svpetry/SP-C64/Keyboard/Chameleon_64_-_PS2_Keymap.jpg

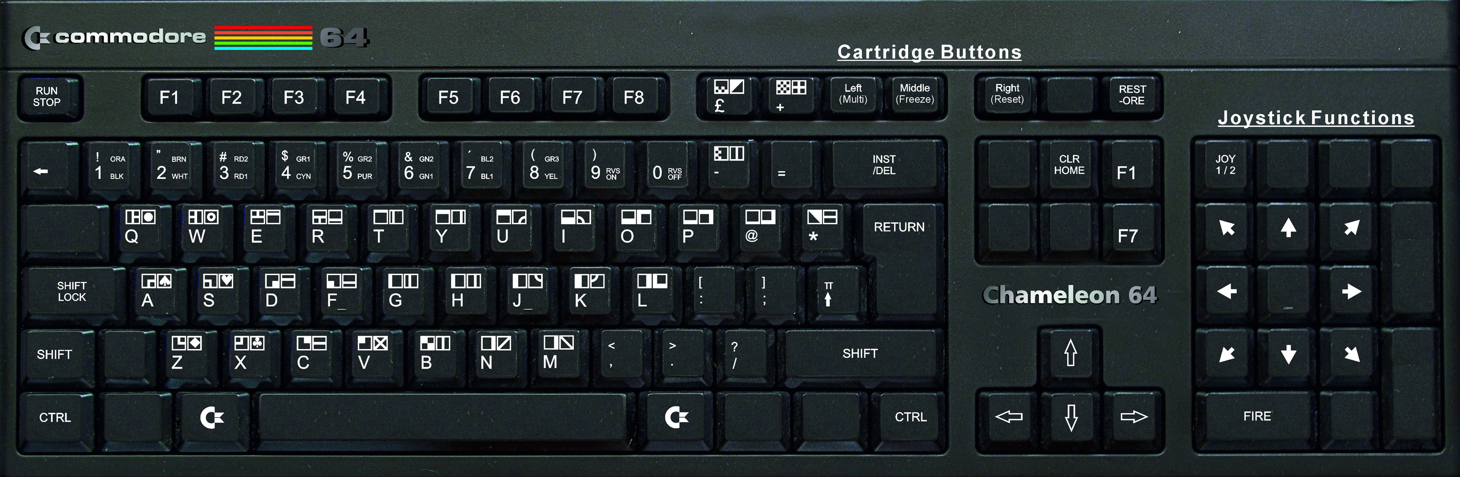
Keyboard/Chameleon_64_-_PS2_Keymap.jpg
