svpetry/SP-C64/CIA/6526-1.gif

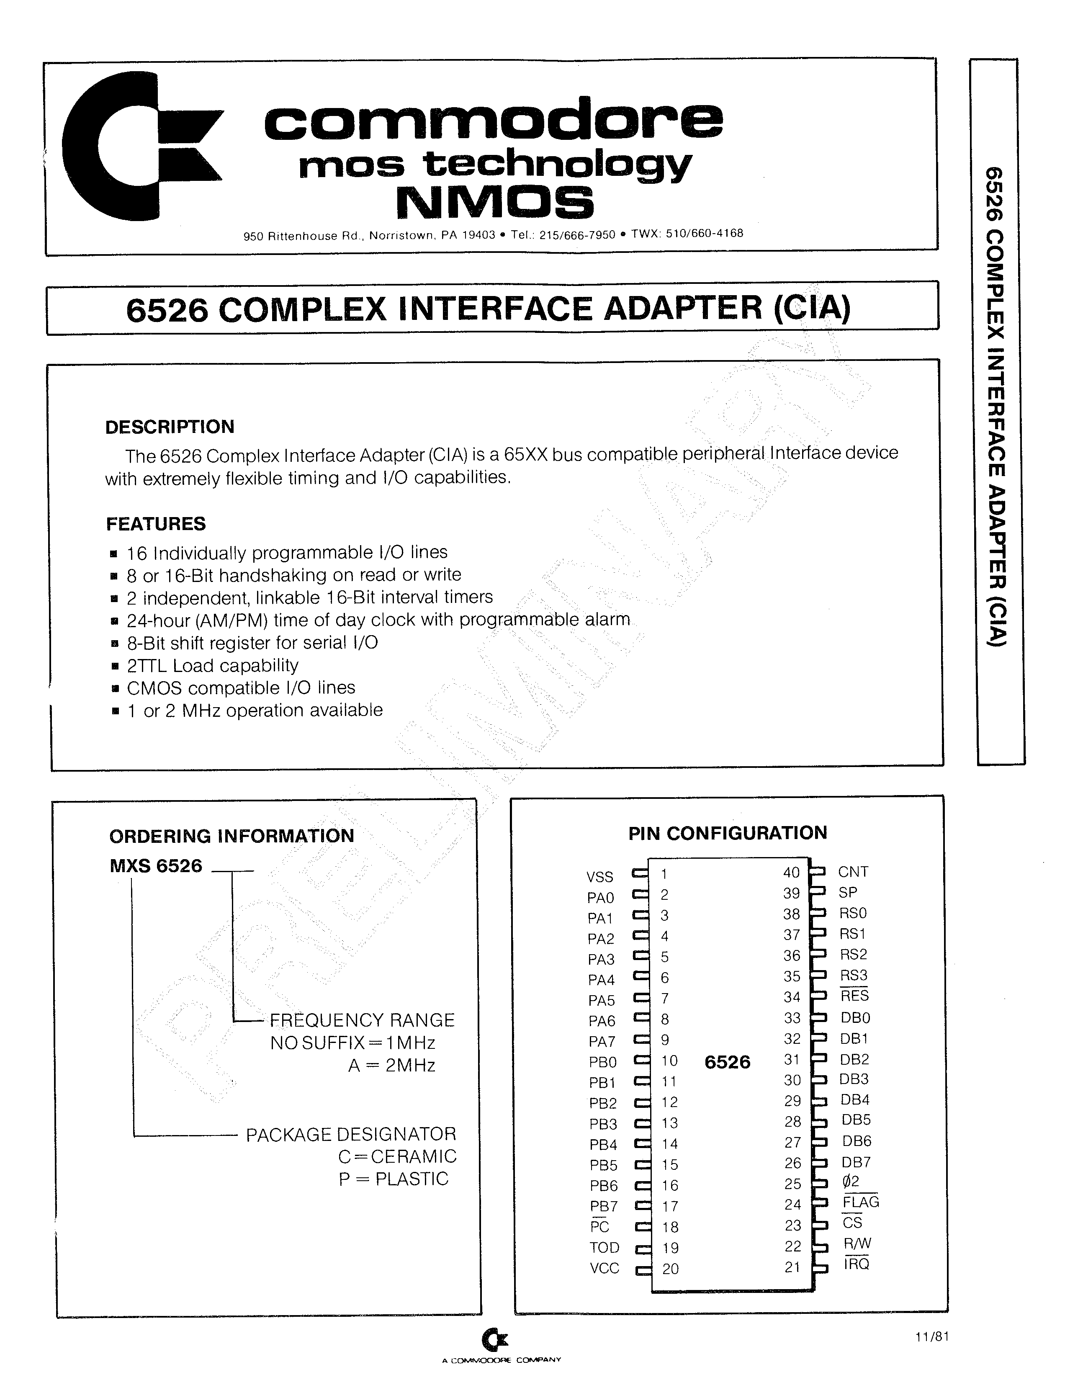
CIA/6526-1.gif
