svpetry/SP-C64/CIA/6526-2.gif

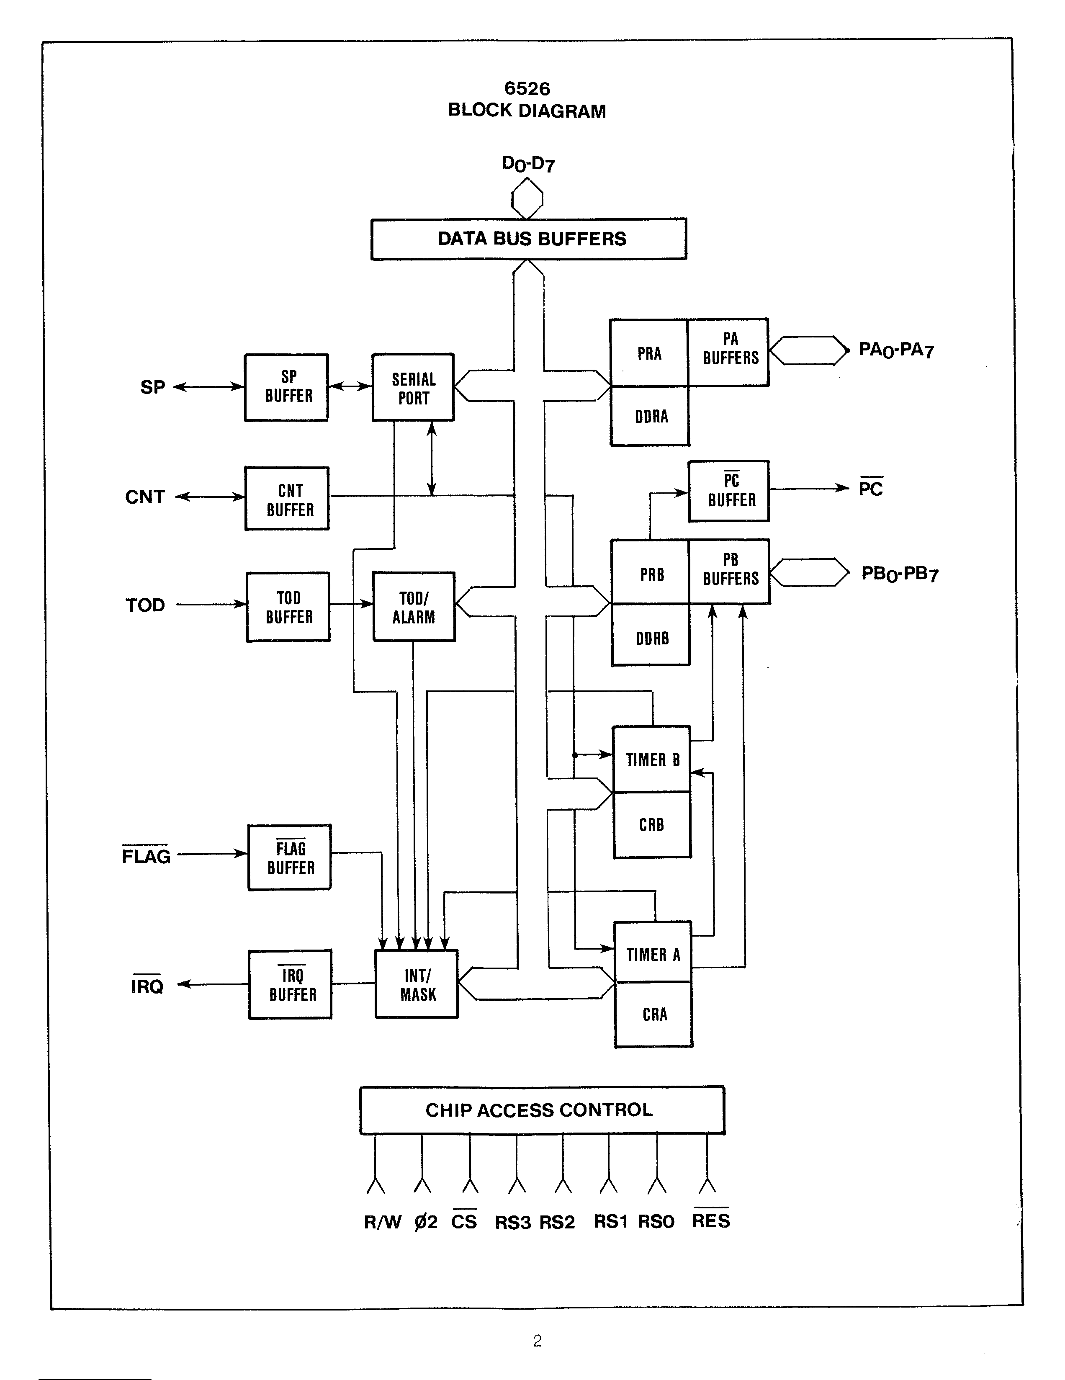
CIA/6526-2.gif
