svpetry/SP-C64/CIA/6526-3.gif

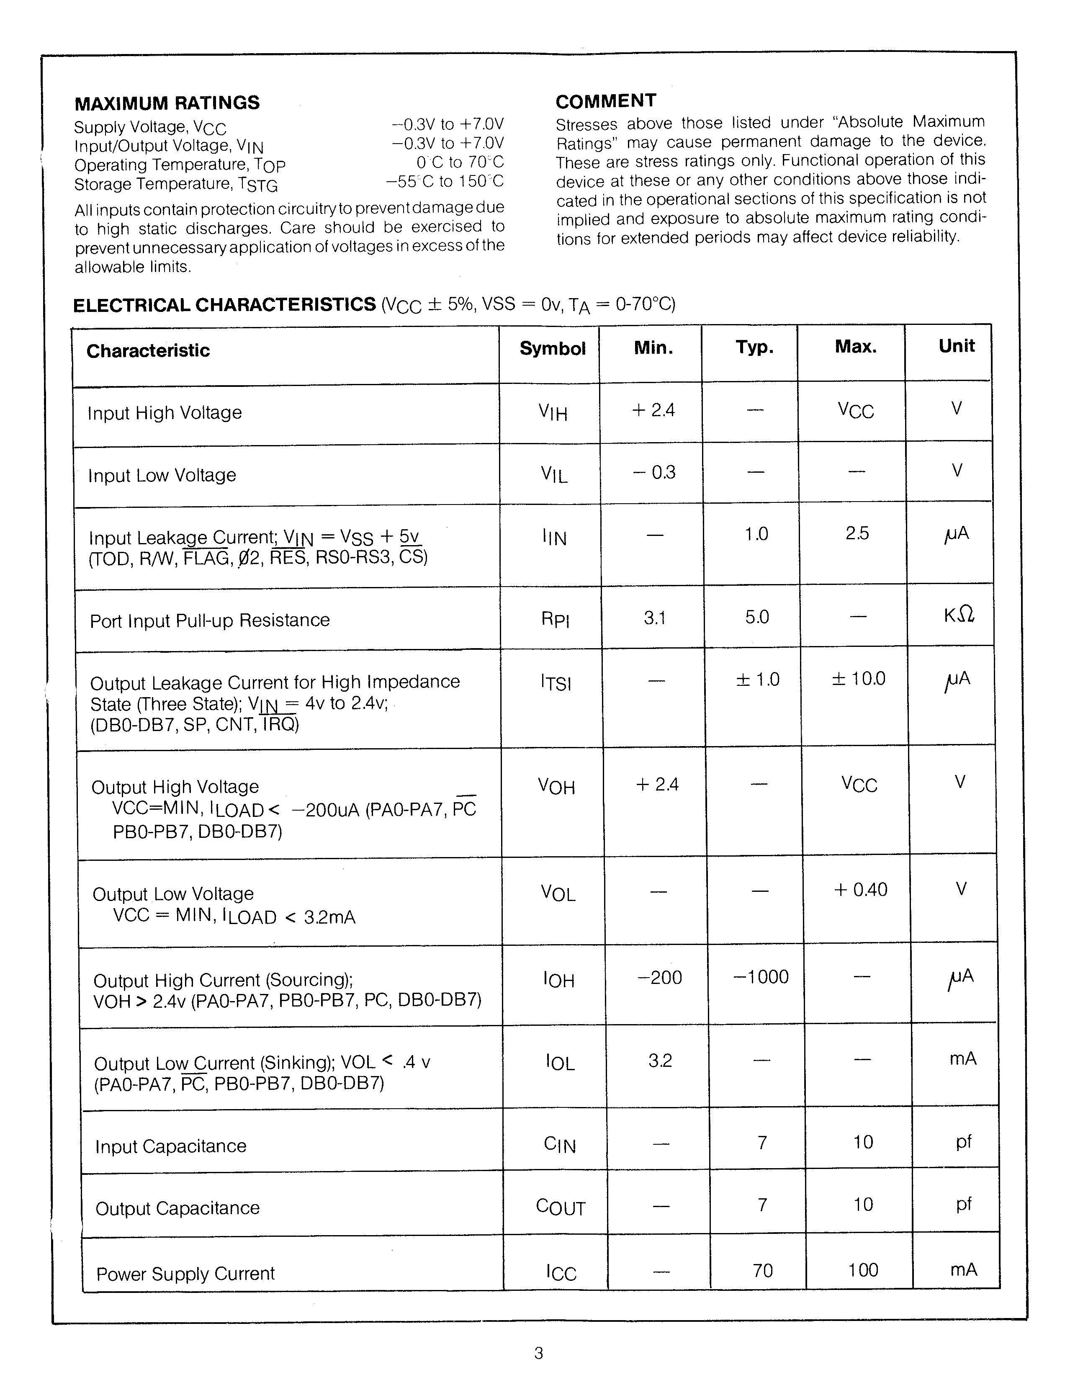
CIA/6526-3.gif
