svpetry/SP-C64/CIA/6526-4.gif

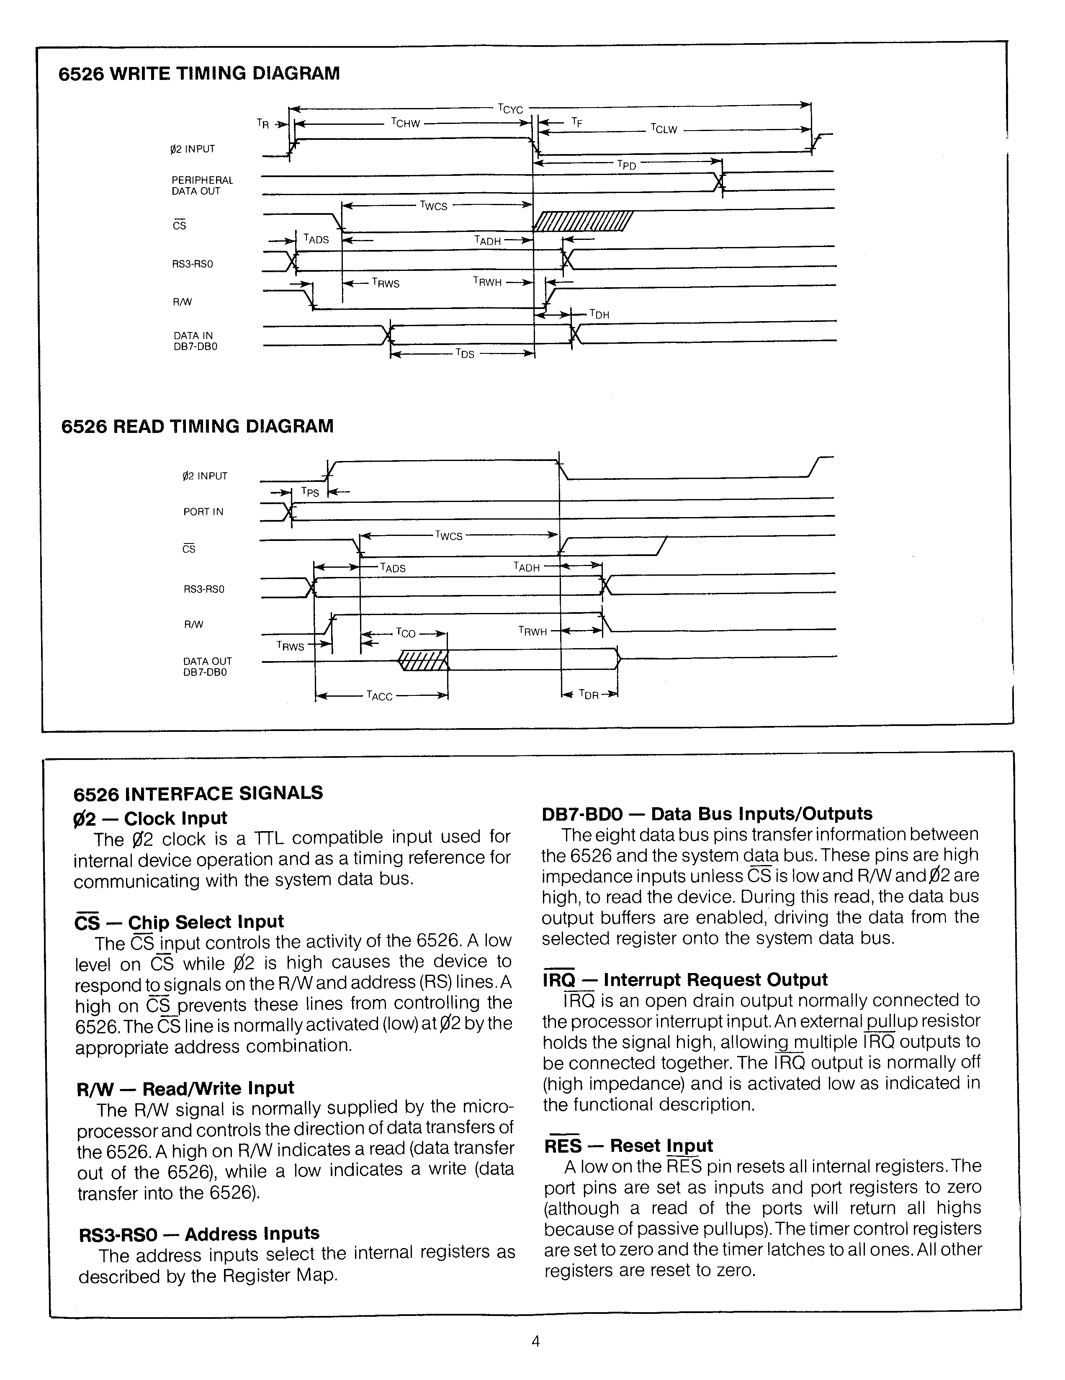
CIA/6526-4.gif
