svpetry/SP-C64/CIA/6526-5.gif

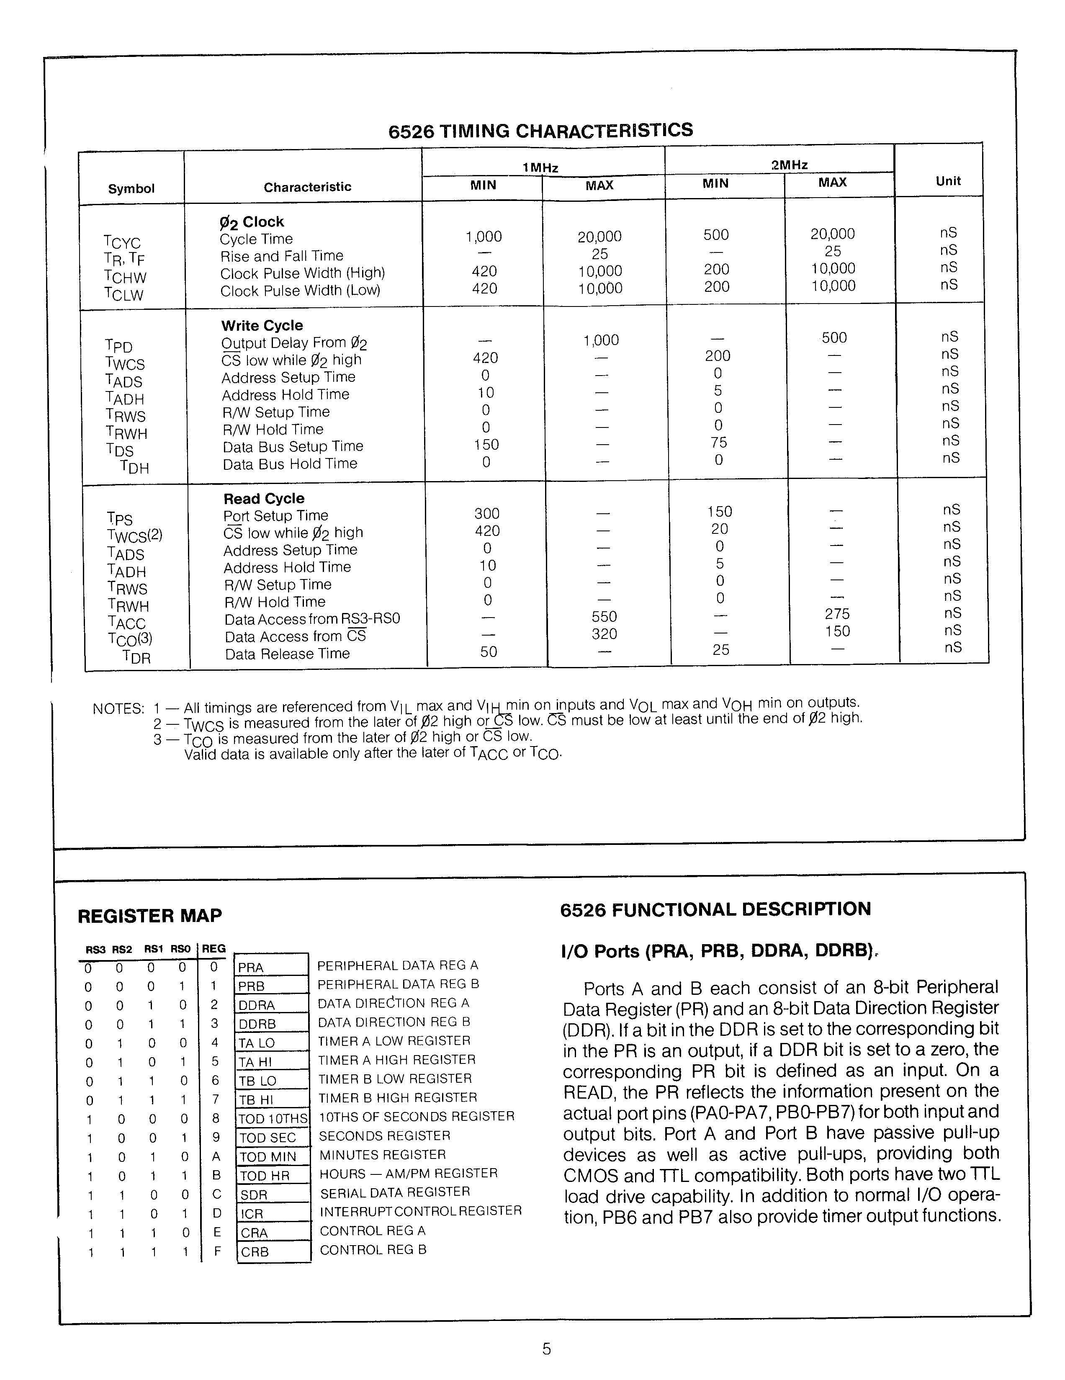
CIA/6526-5.gif
