svpetry/SP-C64/CIA/6526-6.gif

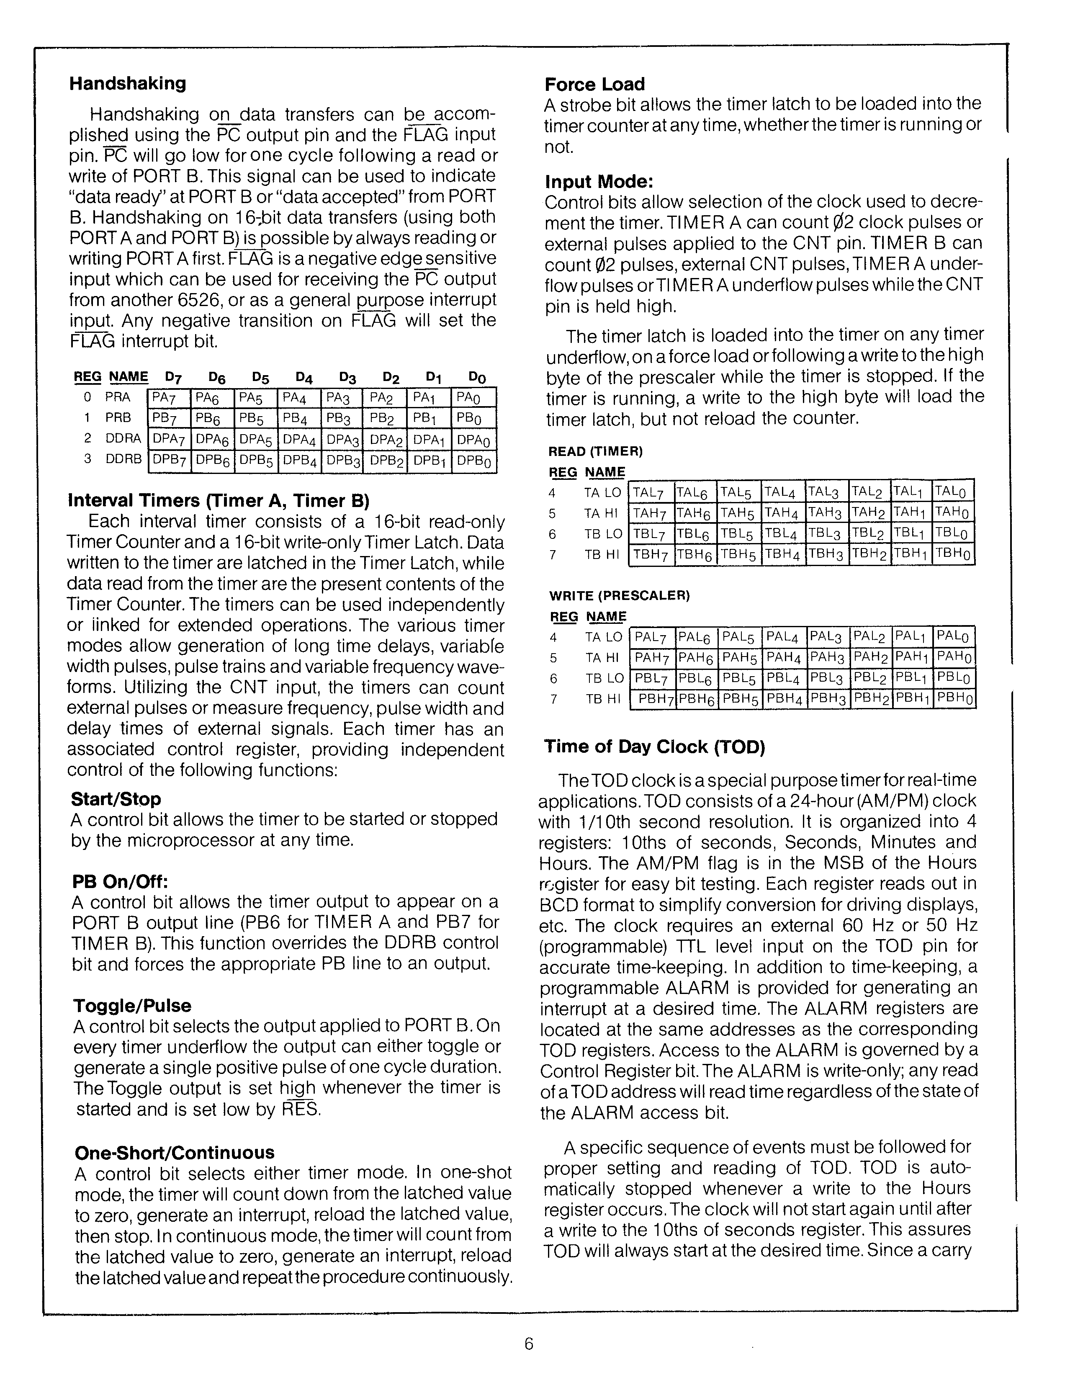
CIA/6526-6.gif
