svpetry/SP-C64/CIA/6526-7.gif

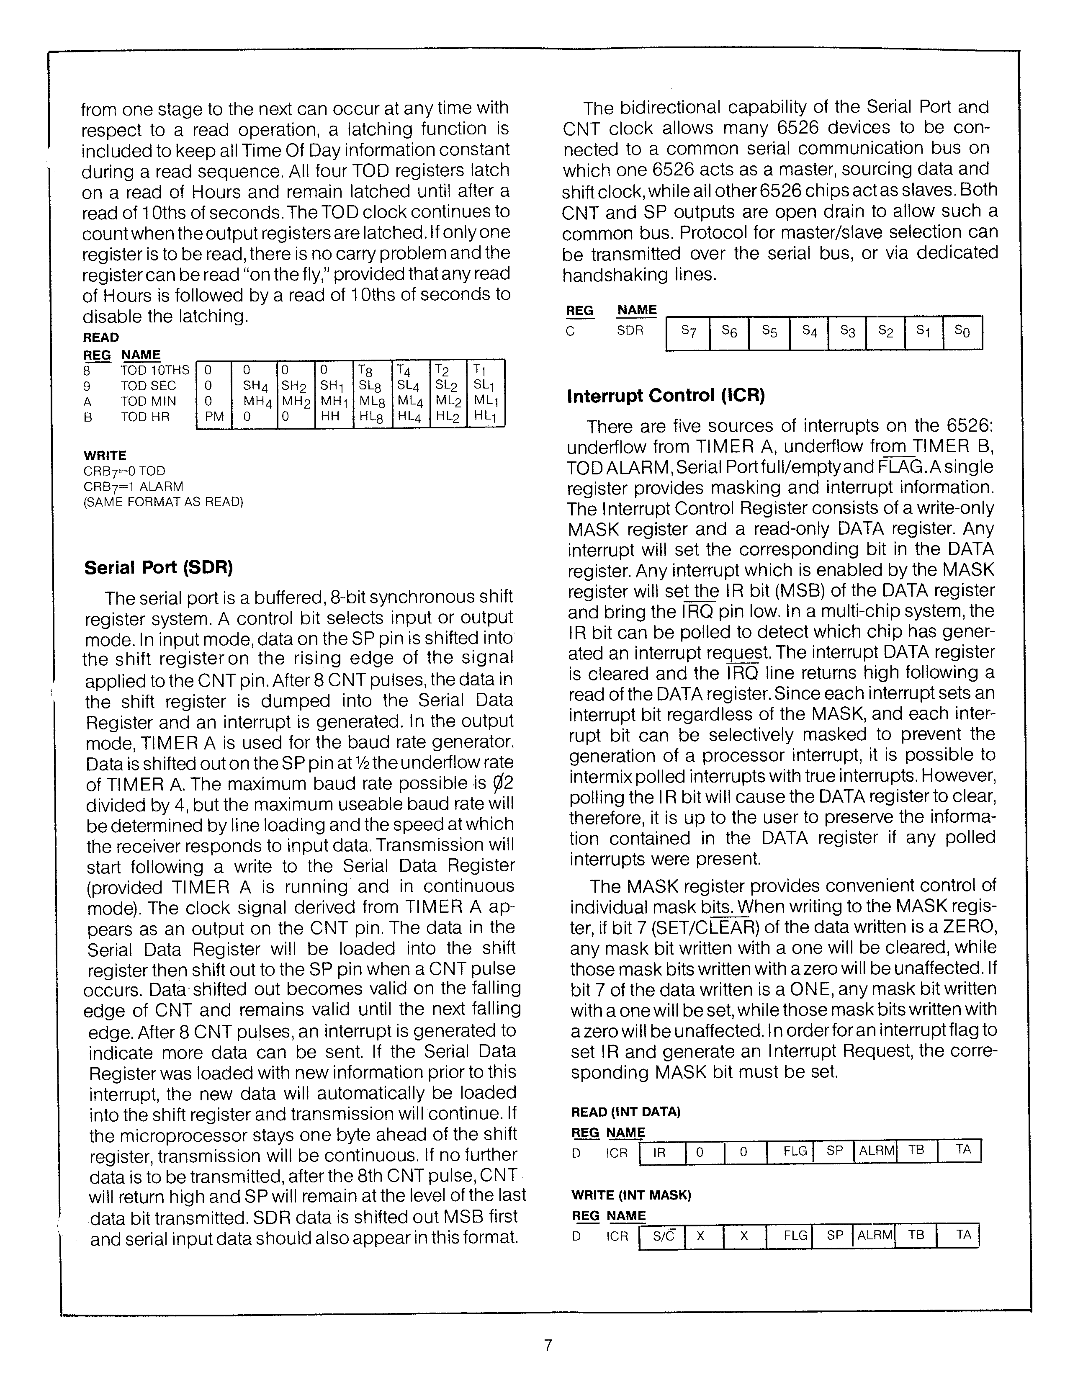
CIA/6526-7.gif
