svpetry/SP-C64/CIA/6526-8.gif

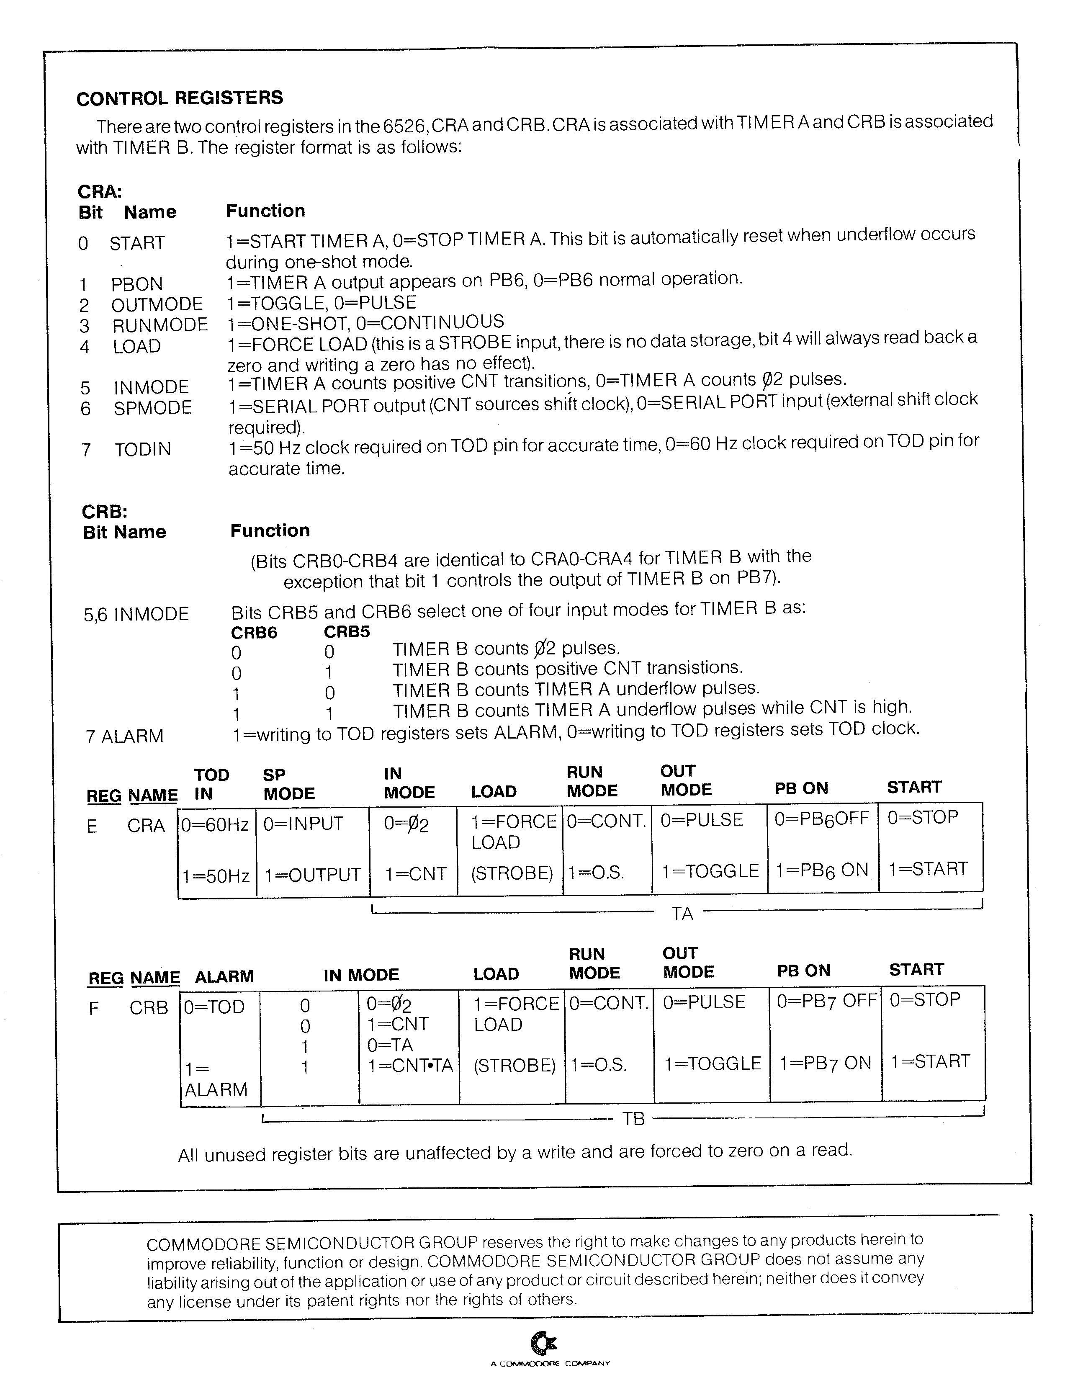
CIA/6526-8.gif
