svpetry/SP-C64/CIA/13114.png

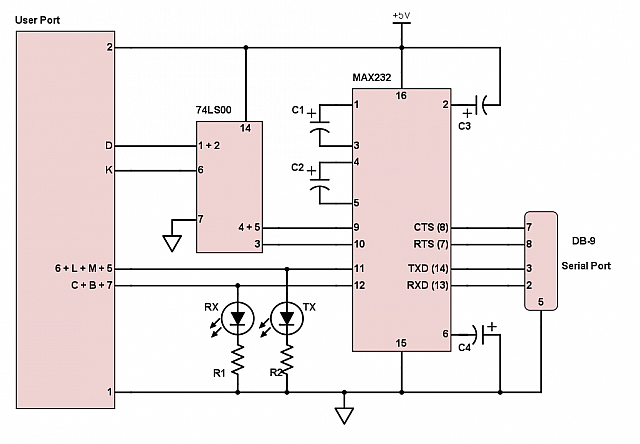
CIA/13114.png
