svpetry/SP-C64/Diagnostic/C64_Diagnostic_324517-02/C64_Diagnostic_324517-02.png

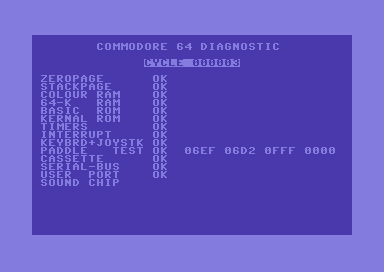
Diagnostic/C64_Diagnostic_324517-02/C64_Diagnostic_324517-02.png
