svpetry/SP-C64/Diagnostic/C64_Diagnostic_324517-02/C64_Diagnostic_schematic.jpg

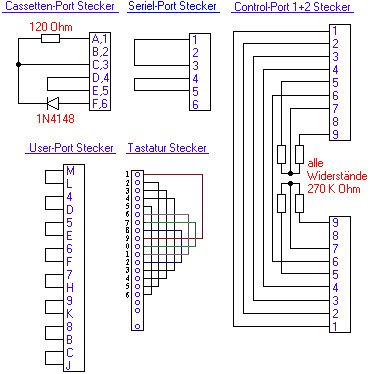
Diagnostic/C64_Diagnostic_324517-02/C64_Diagnostic_schematic.jpg
