svpetry/SP-C64/Diagnostic/Diag_586220/C64_Diag_586220_Harness_schem1.png

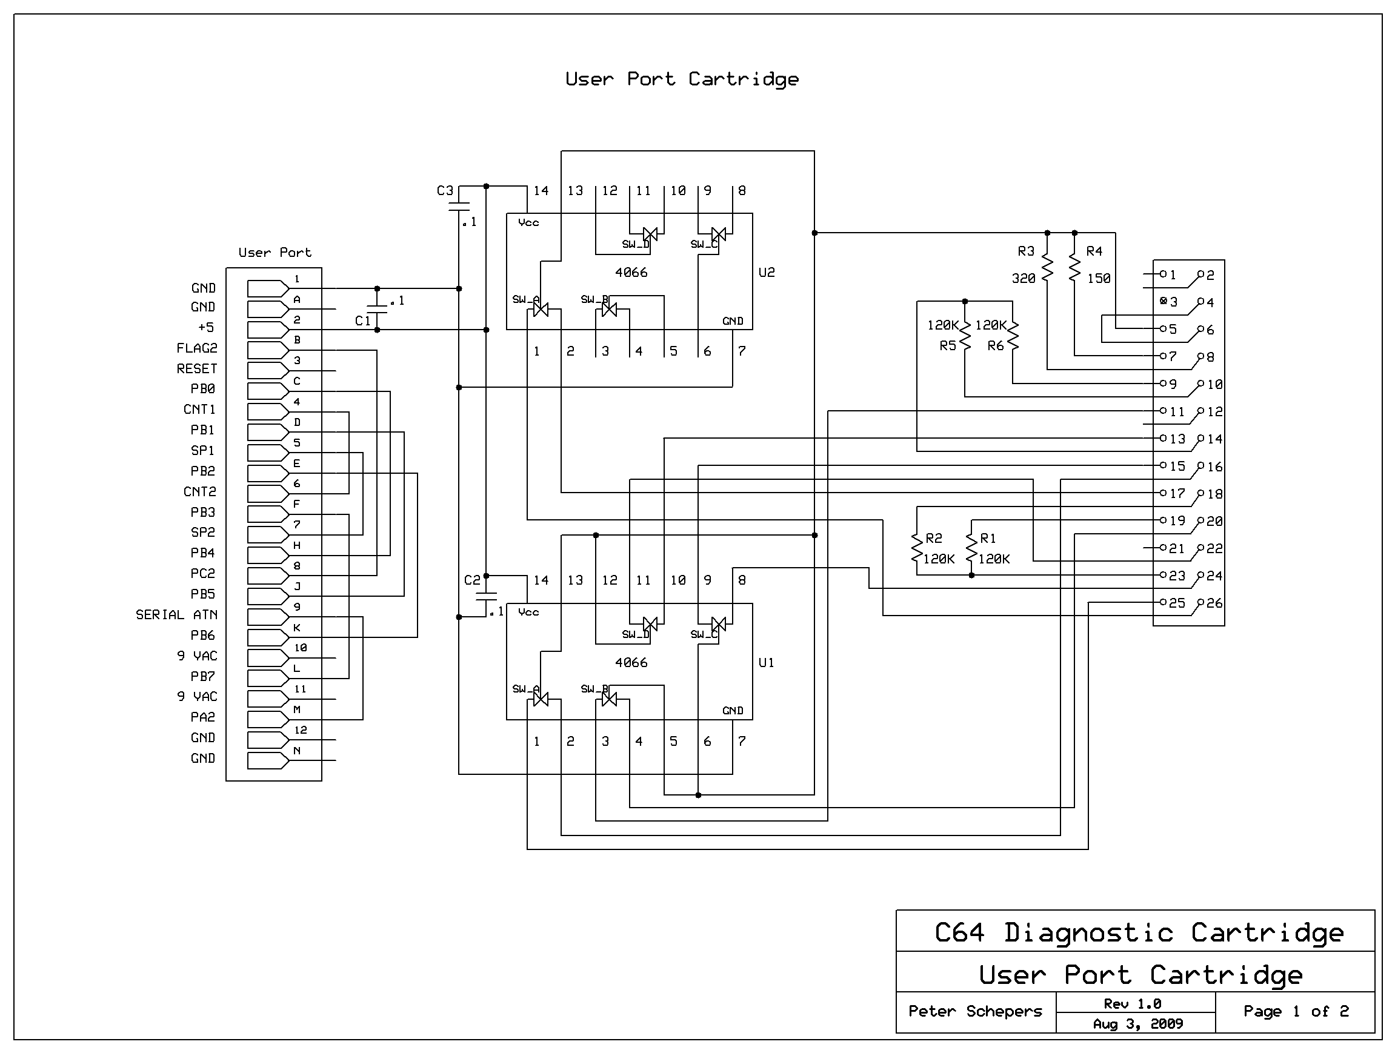
Diagnostic/Diag_586220/C64_Diag_586220_Harness_schem1.png
