svpetry/SP-C64/Diagnostic/Diag_586220/diag-c64_586220.png

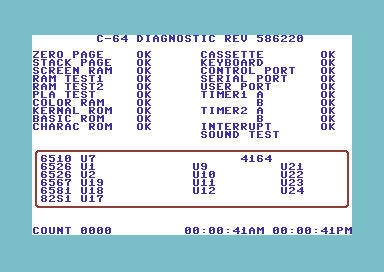
Diagnostic/Diag_586220/diag-c64_586220.png
