svpetry/SP-C64/Keyboard/keybconn.gif

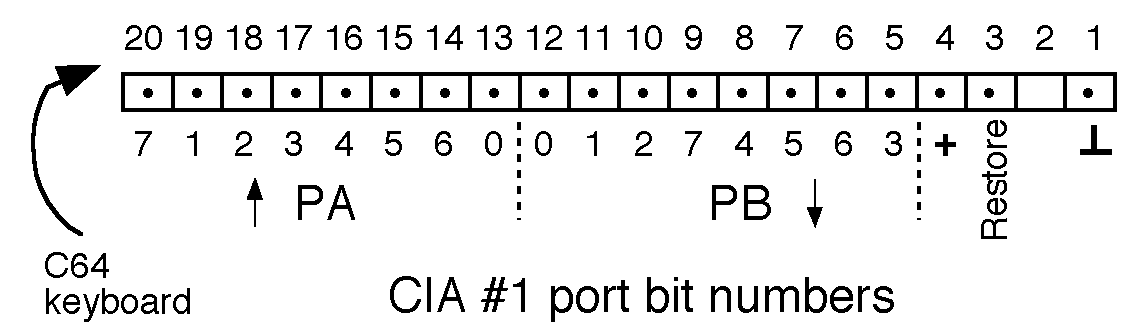
Keyboard/keybconn.gif
