svpetry/SP-C64/Keyboard/scancod1.gif

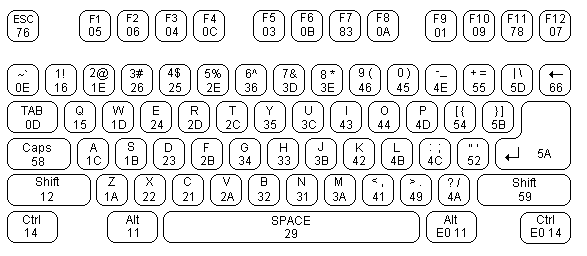
Keyboard/scancod1.gif
