svpetry/SP-C64/Keyboard/scancodes.gif

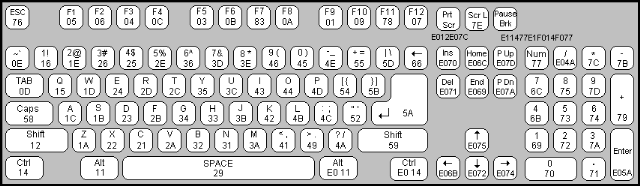
Keyboard/scancodes.gif
