svpetry/SP-C64/Keyboard/uskeyb.gif

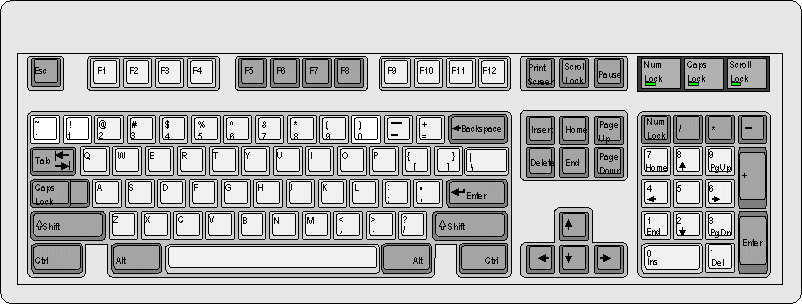
Keyboard/uskeyb.gif
