svpetry/SP-C64/PLA/PLA_IO.png

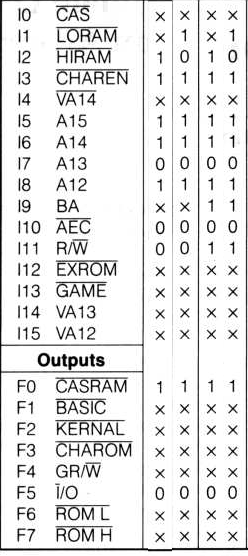
PLA/PLA_IO.png
