svpetry/SP-C64/RAM/georam-sch.png

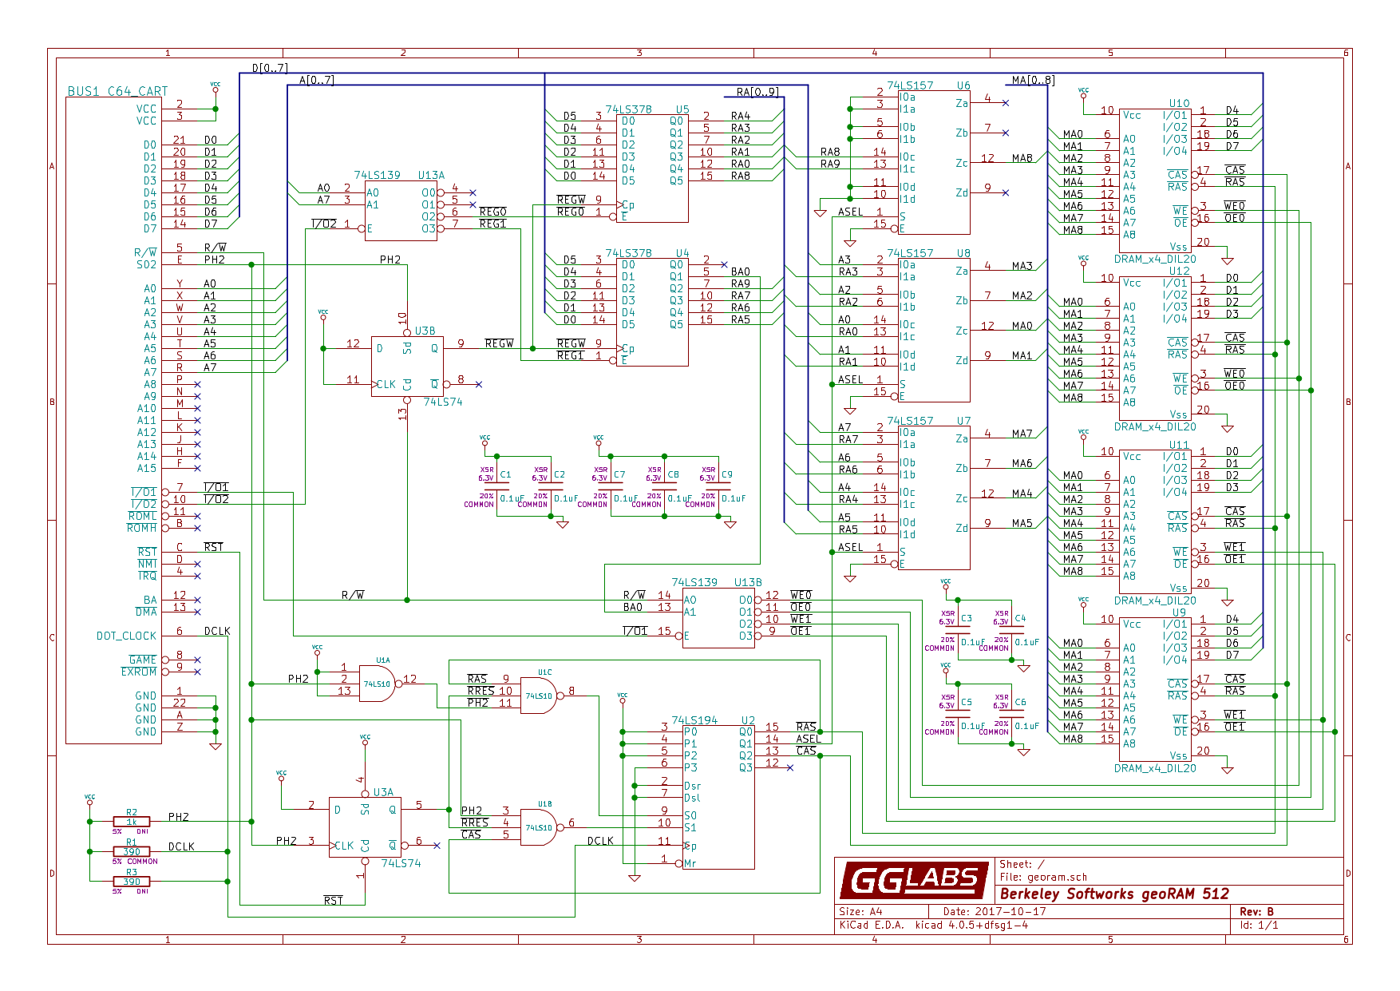
RAM/georam-sch.png
