svpetry/SP-C64/RAM/neoram-level2c.png

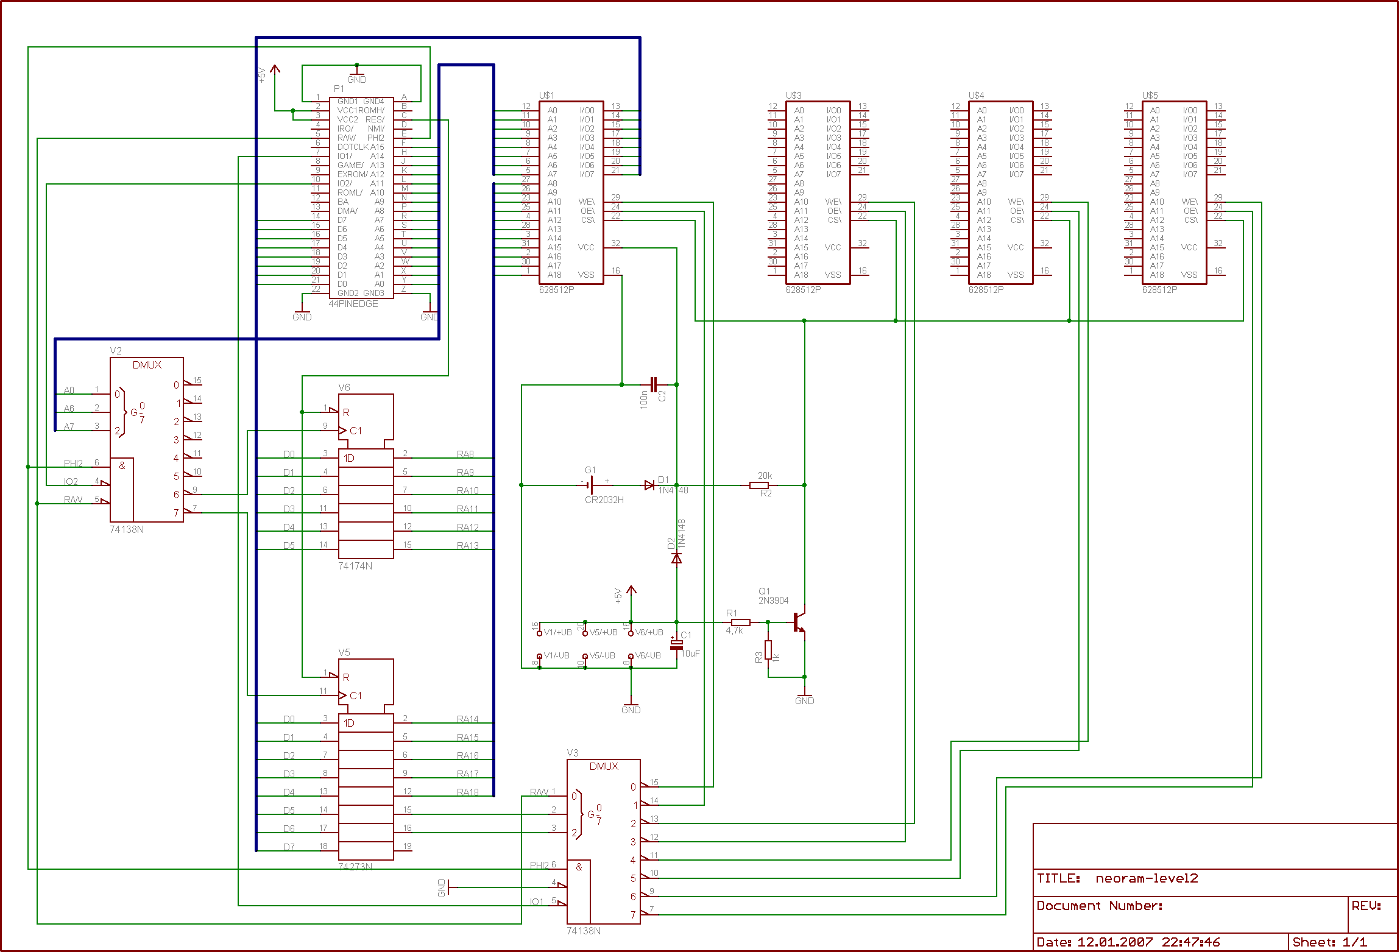
RAM/neoram-level2c.png
