svpetry/SP-C64/RAM/SRAM.png

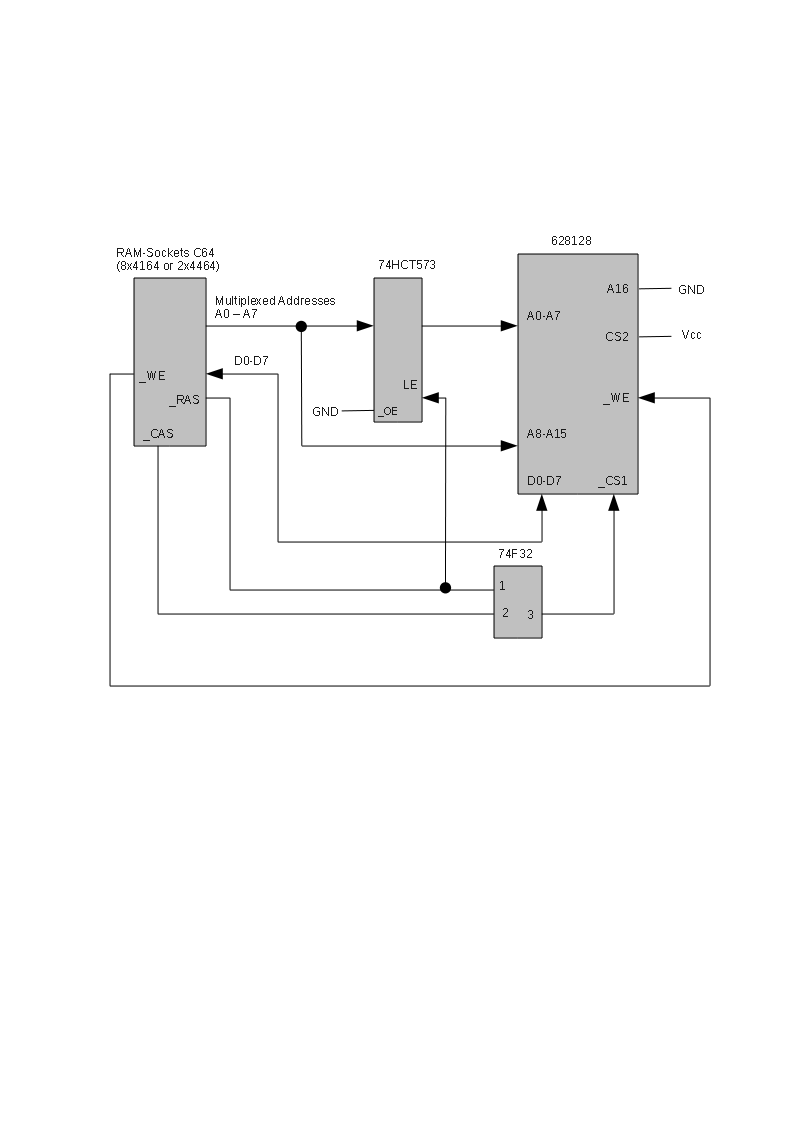
RAM/SRAM.png
