svpetry/SP-C64/Schematics/mem.gif

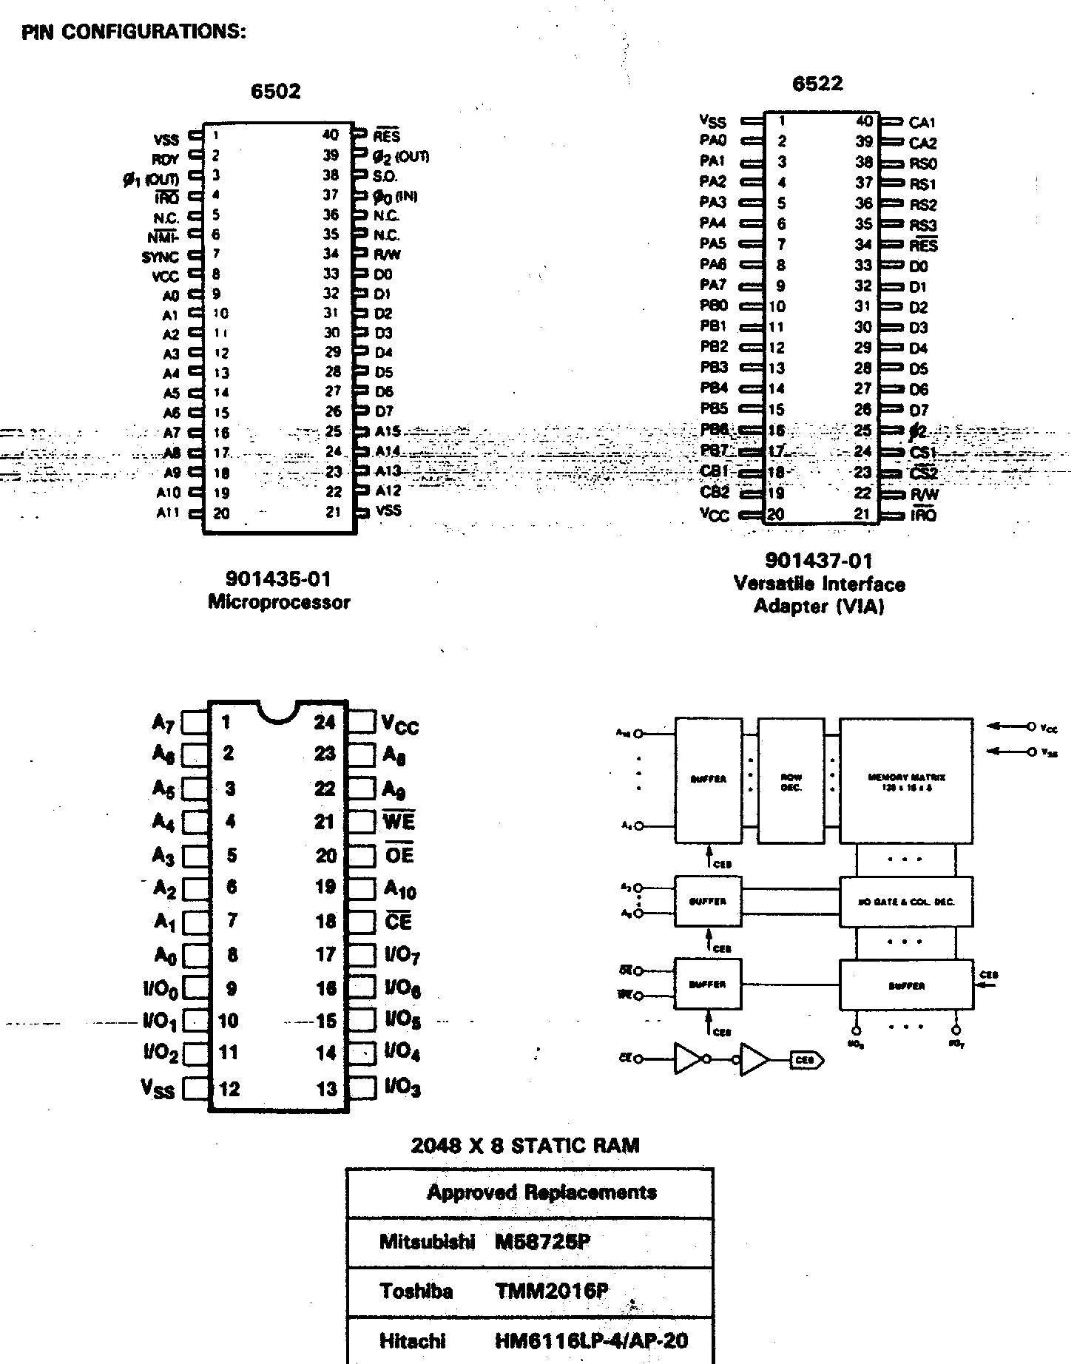
Schematics/mem.gif
