svpetry/SP-C64/VIC/6567/6567-01.GIF

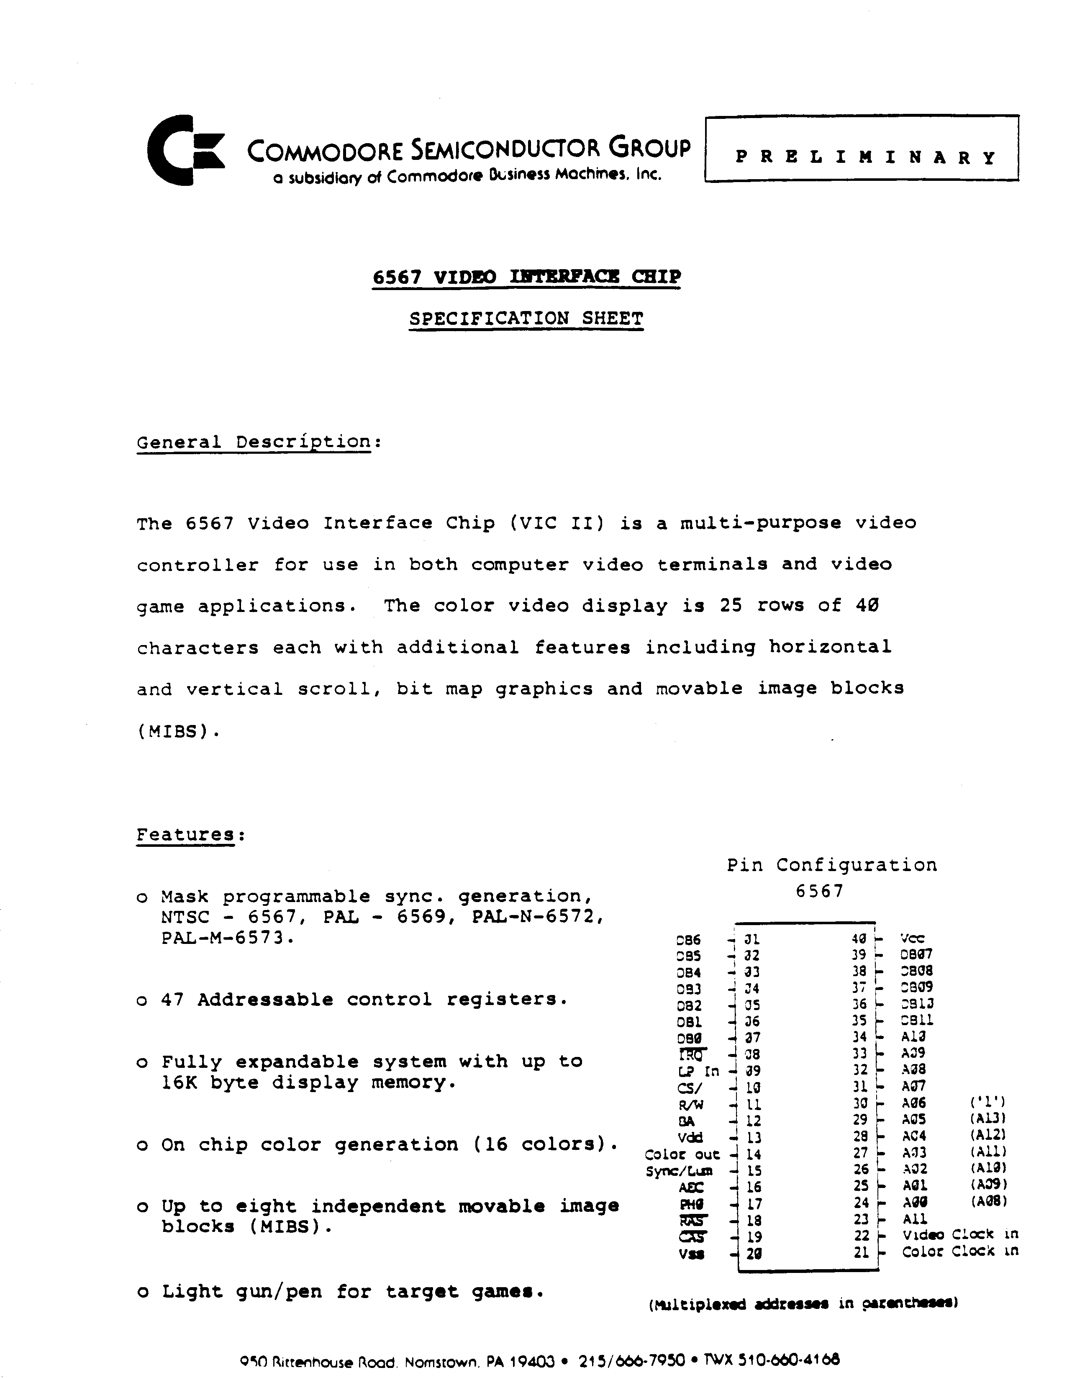
VIC/6567/6567-01.GIF
