svpetry/SP-C64/VIC/6567/6567-02.GIF

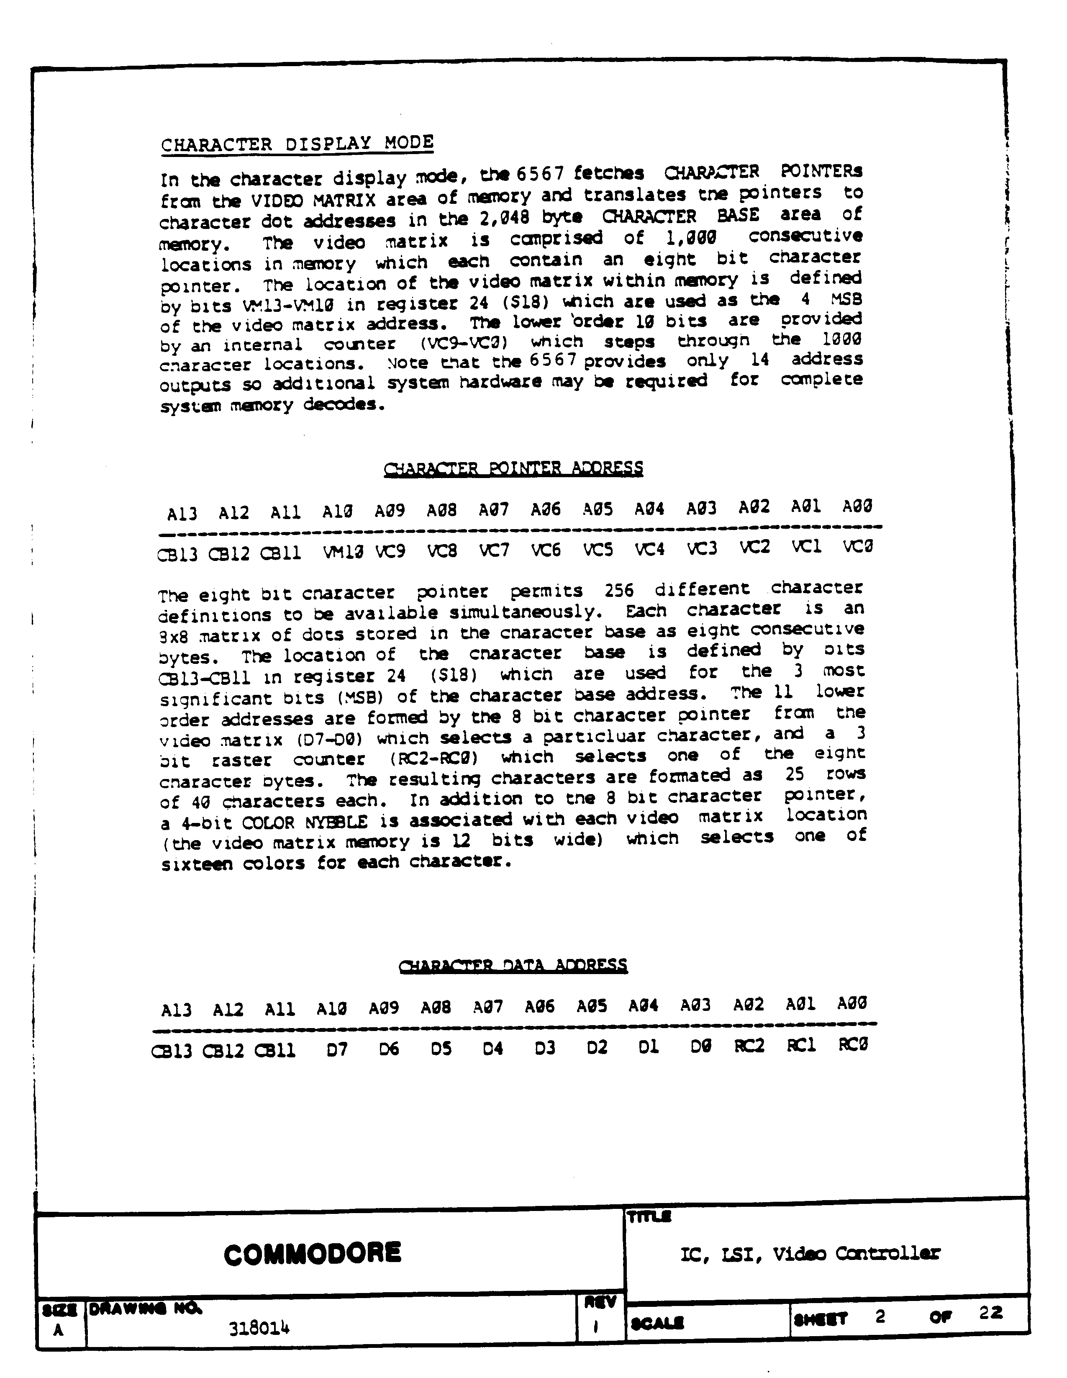
VIC/6567/6567-02.GIF
