svpetry/SP-C64/VIC/6567/6567-04.GIF

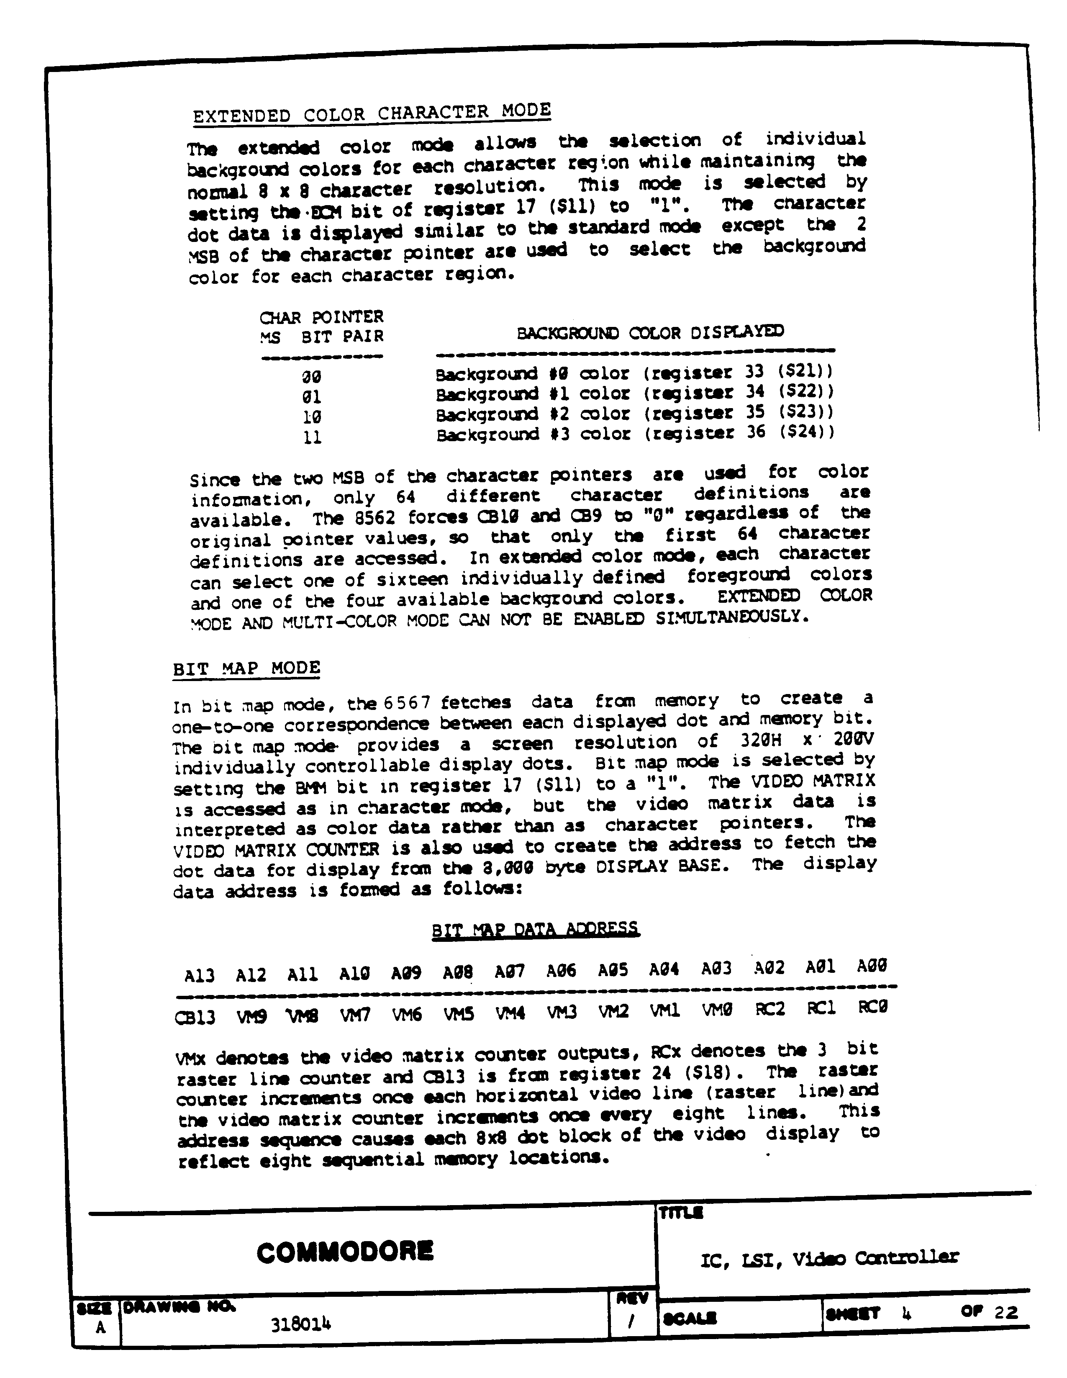
VIC/6567/6567-04.GIF
