svpetry/SP-C64/VIC/6567/6567-07.GIF

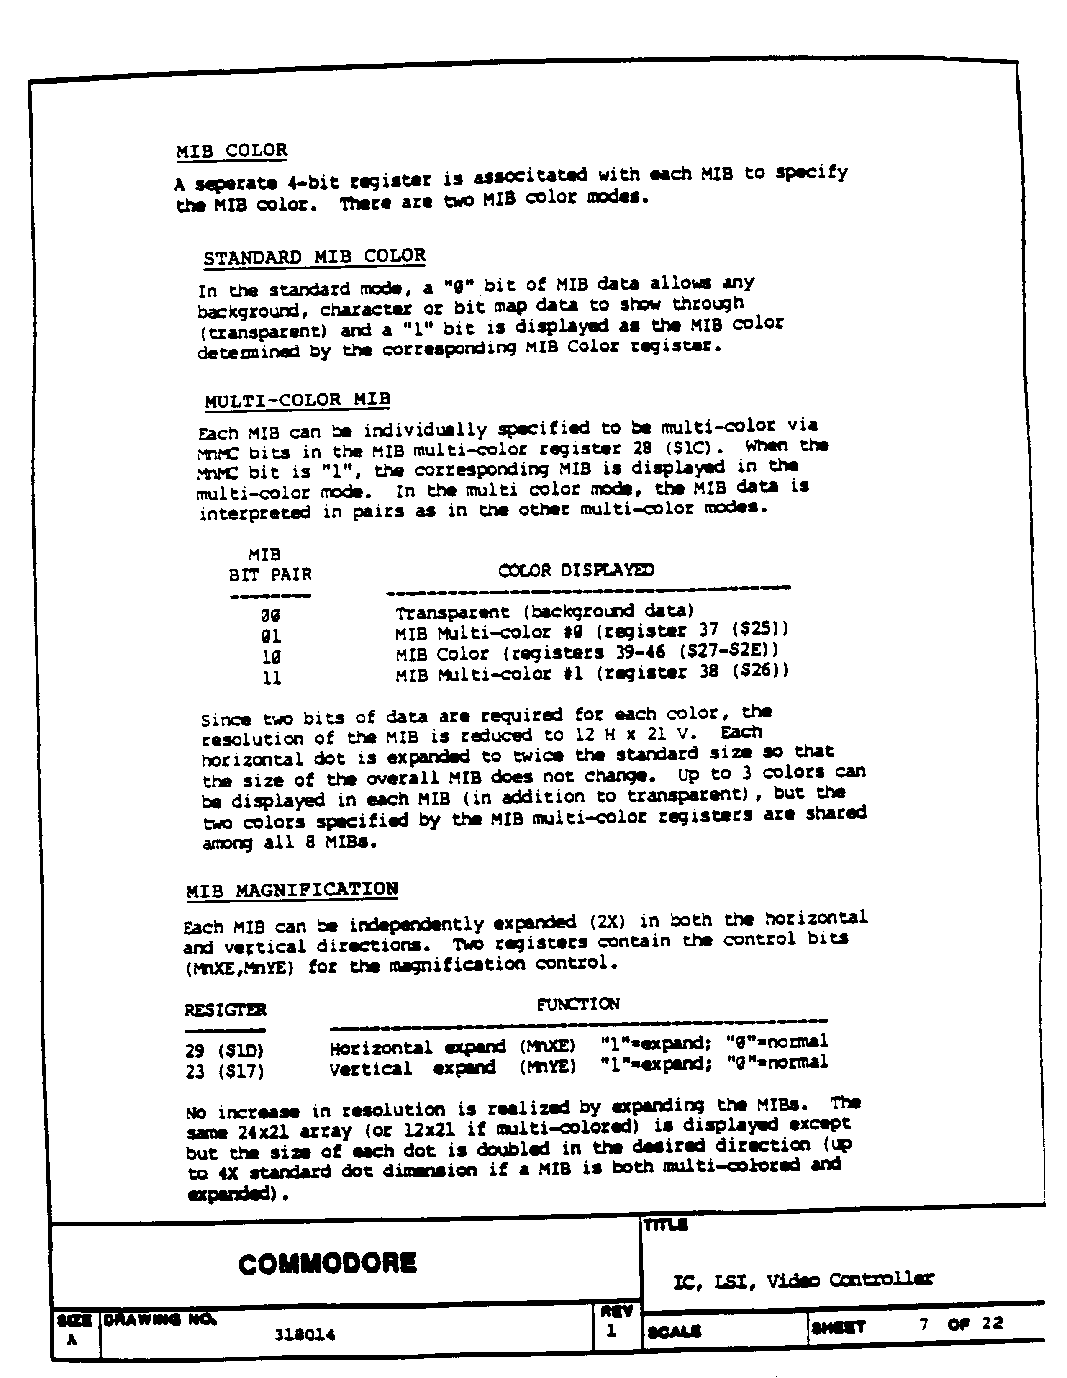
VIC/6567/6567-07.GIF
