svpetry/SP-C64/VIC/6567/6567-09.GIF

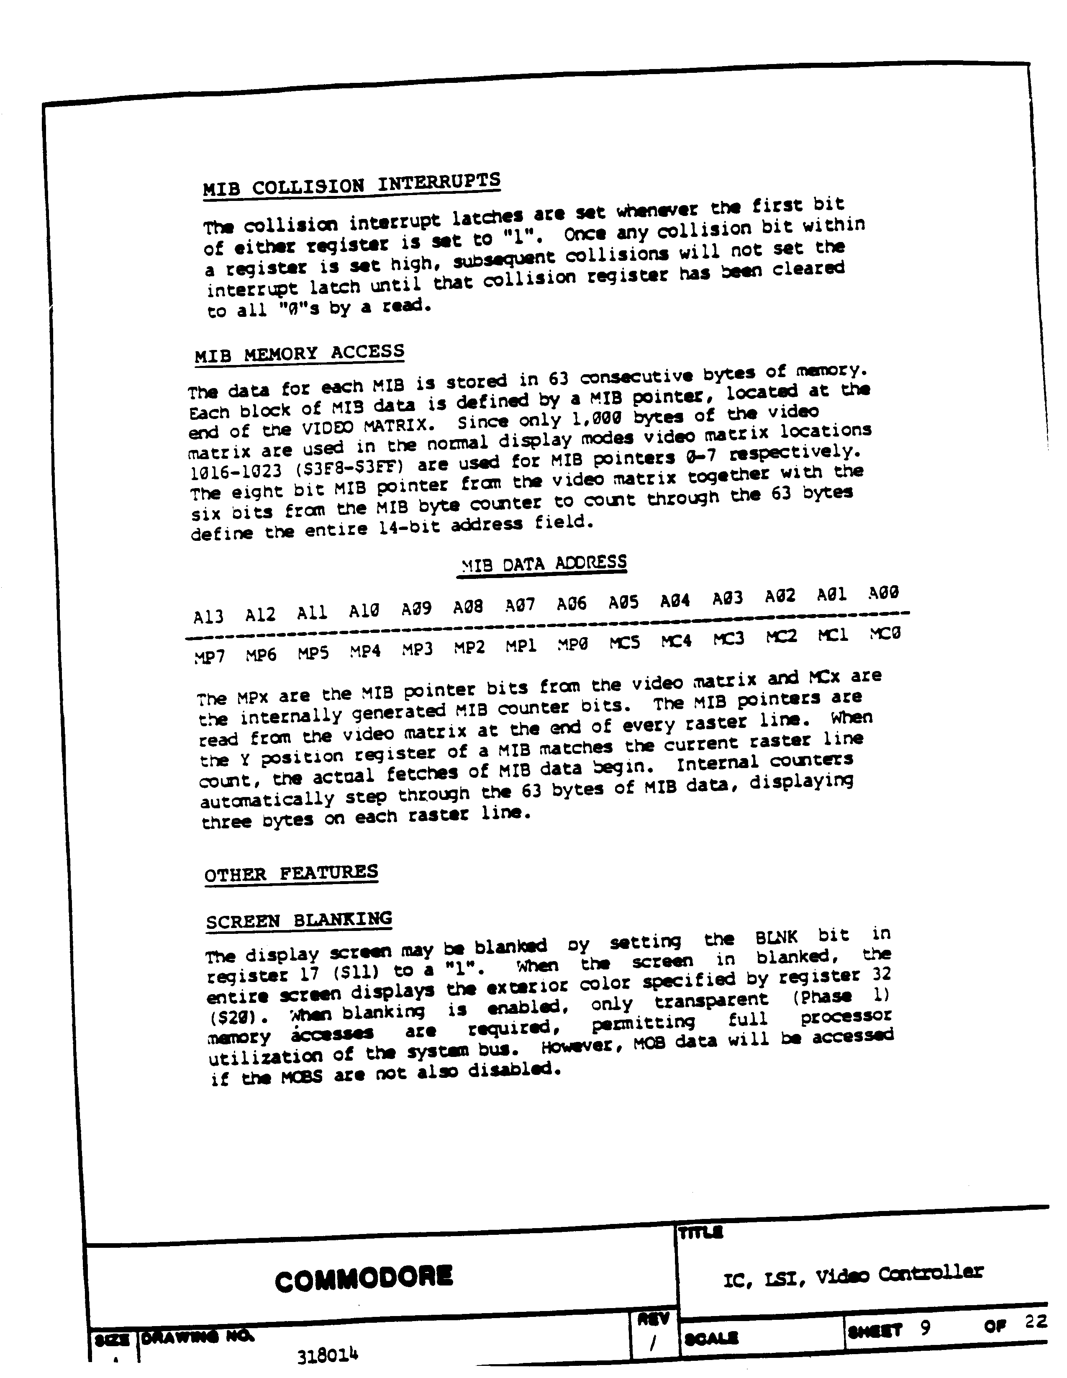
VIC/6567/6567-09.GIF
