svpetry/SP-C64/VIC/6567/6567-10.GIF

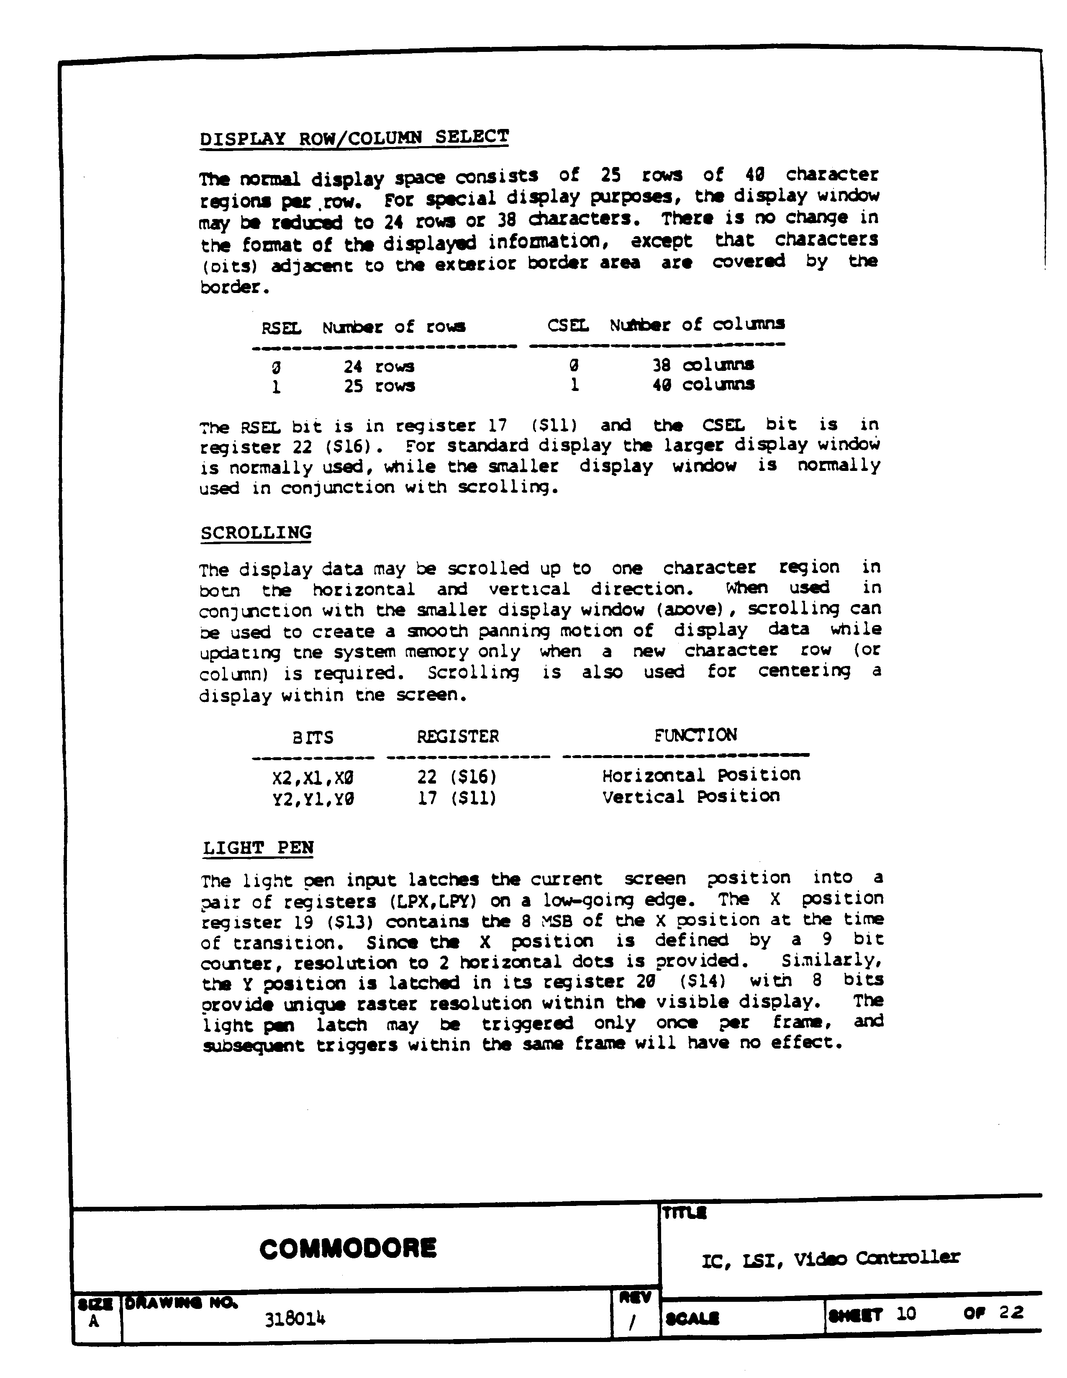
VIC/6567/6567-10.GIF
