svpetry/SP-C64/VIC/6567/6567-12.GIF

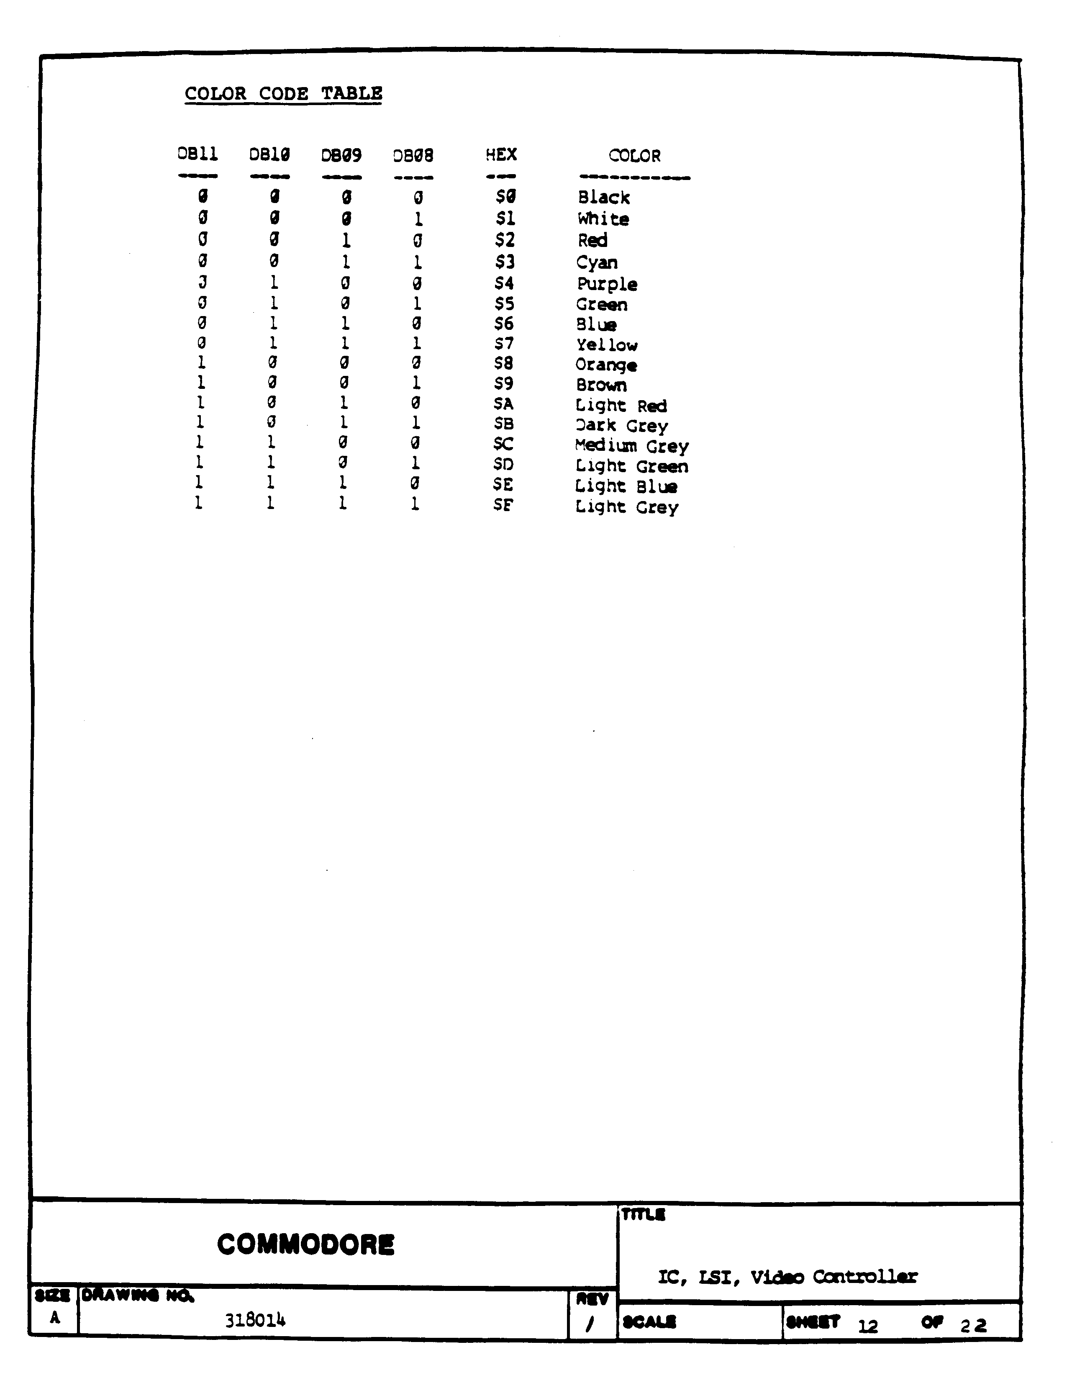
VIC/6567/6567-12.GIF
