svpetry/SP-C64/VIC/6567/6567-13.GIF

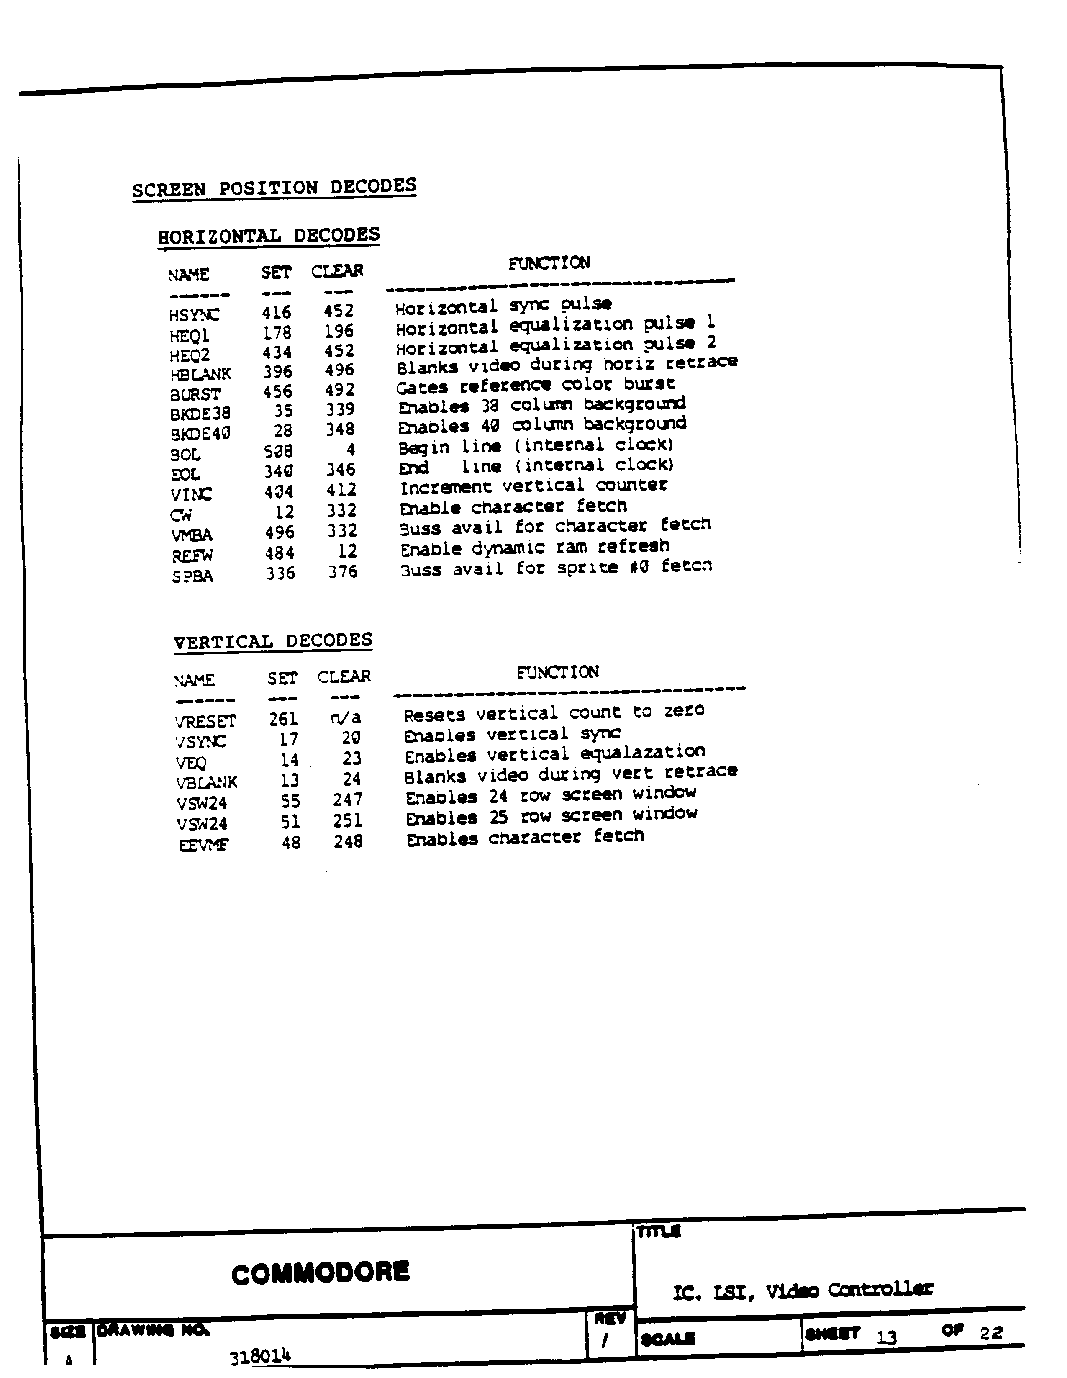
VIC/6567/6567-13.GIF
