svpetry/SP-C64/VIC/6567/6567-15.GIF

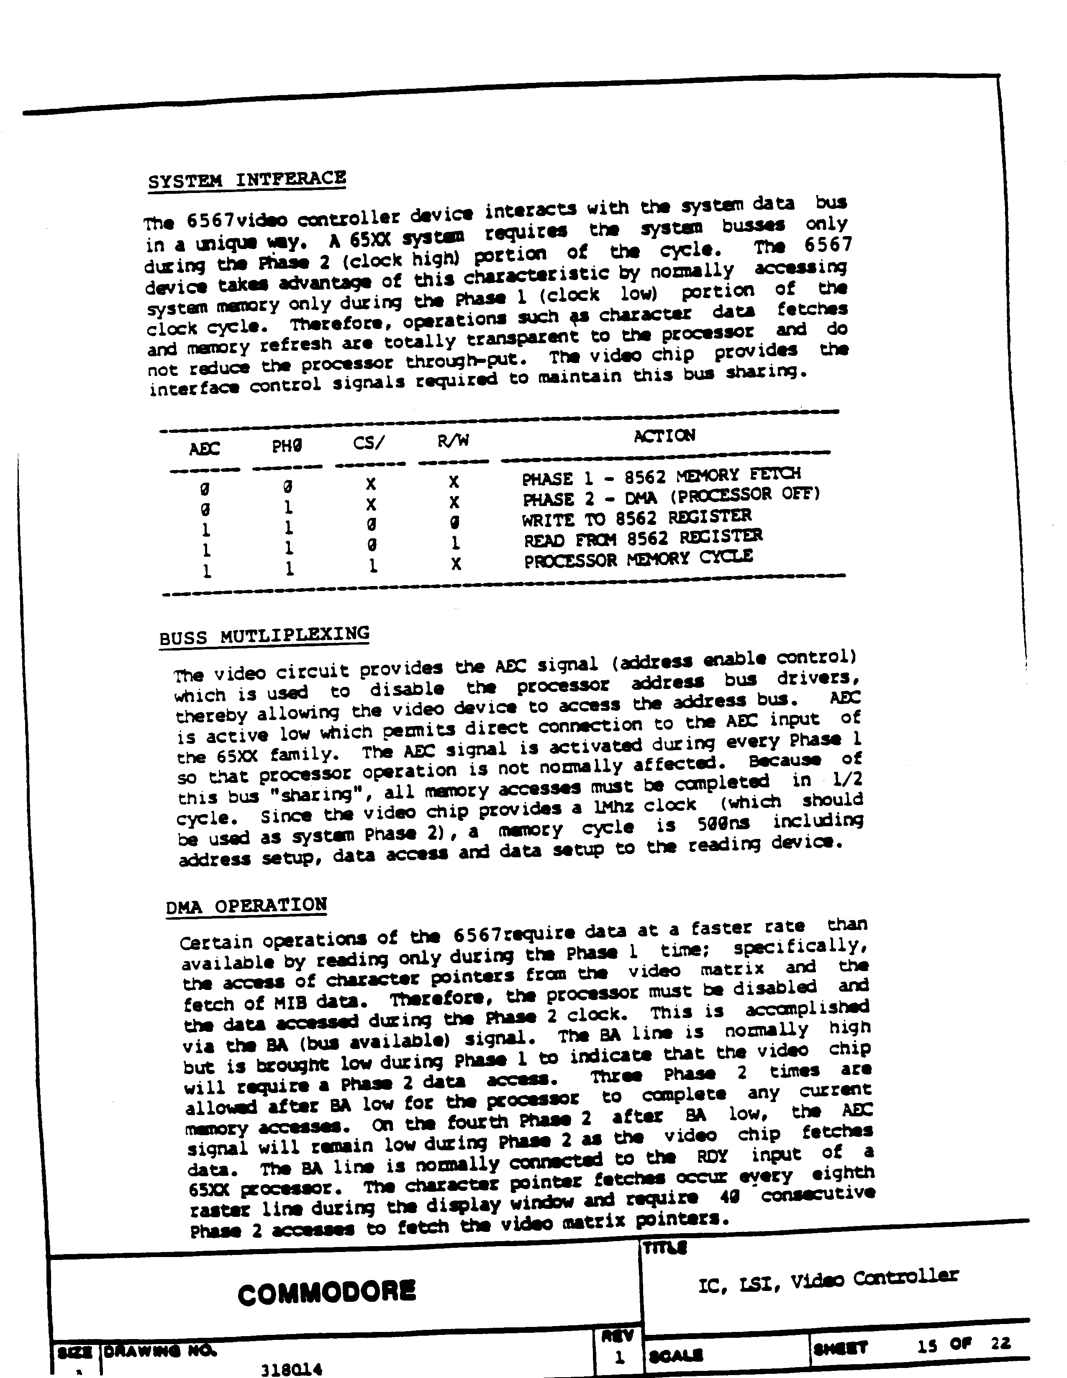
VIC/6567/6567-15.GIF
