svpetry/SP-C64/VIC/6567/6567-18.GIF

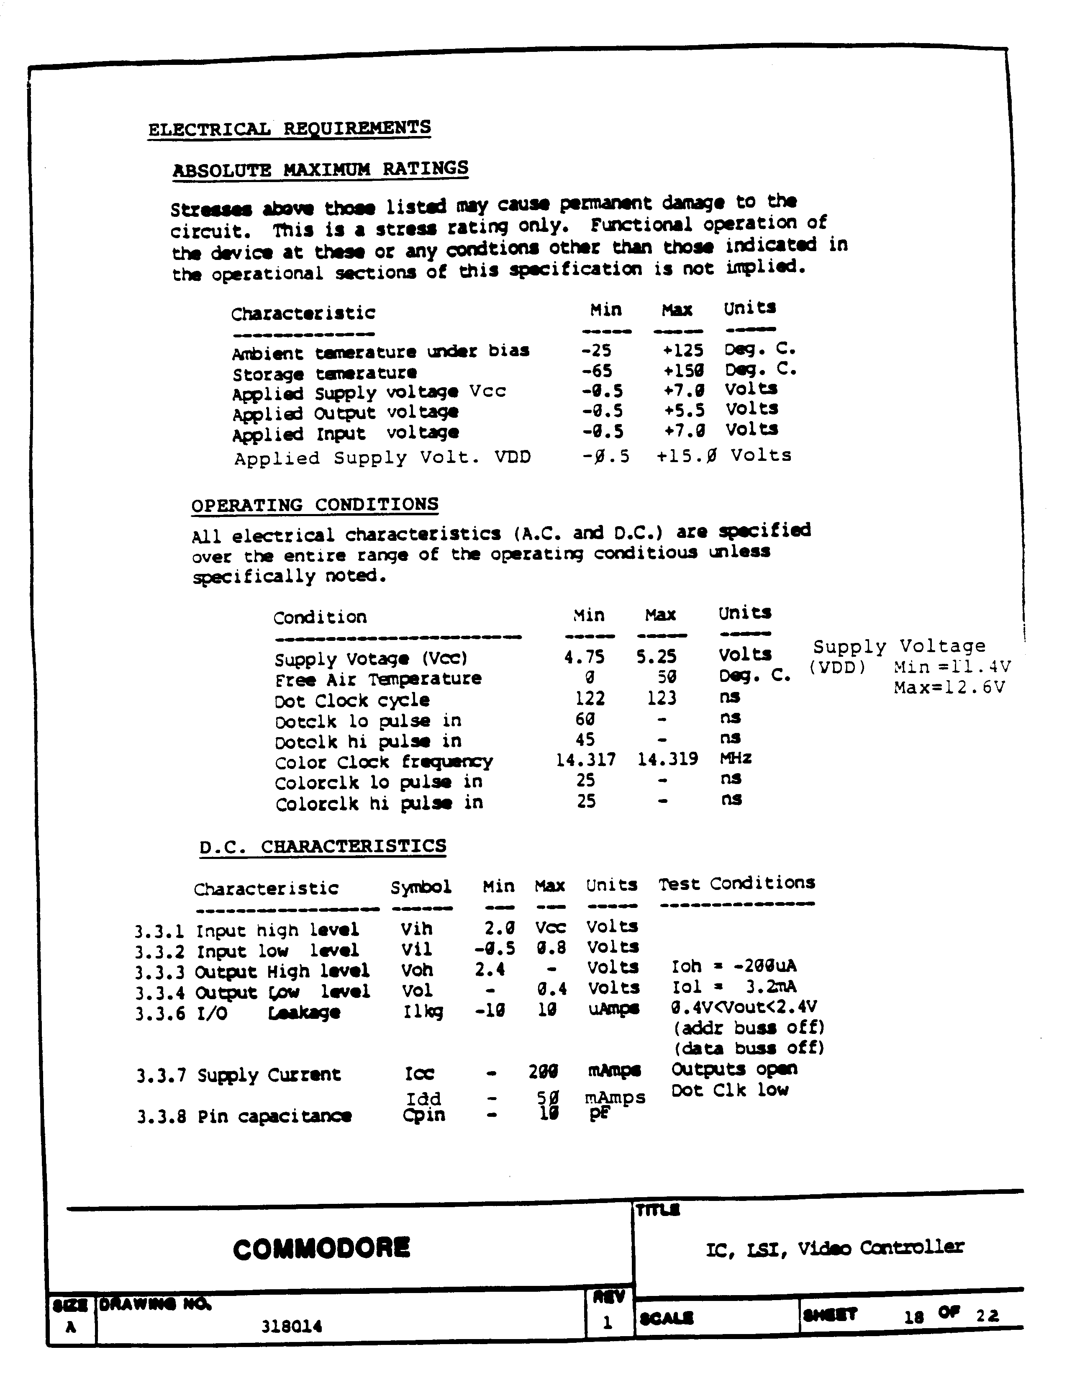
VIC/6567/6567-18.GIF
