svpetry/SP-C64/VIC/6567/6567-21.GIF

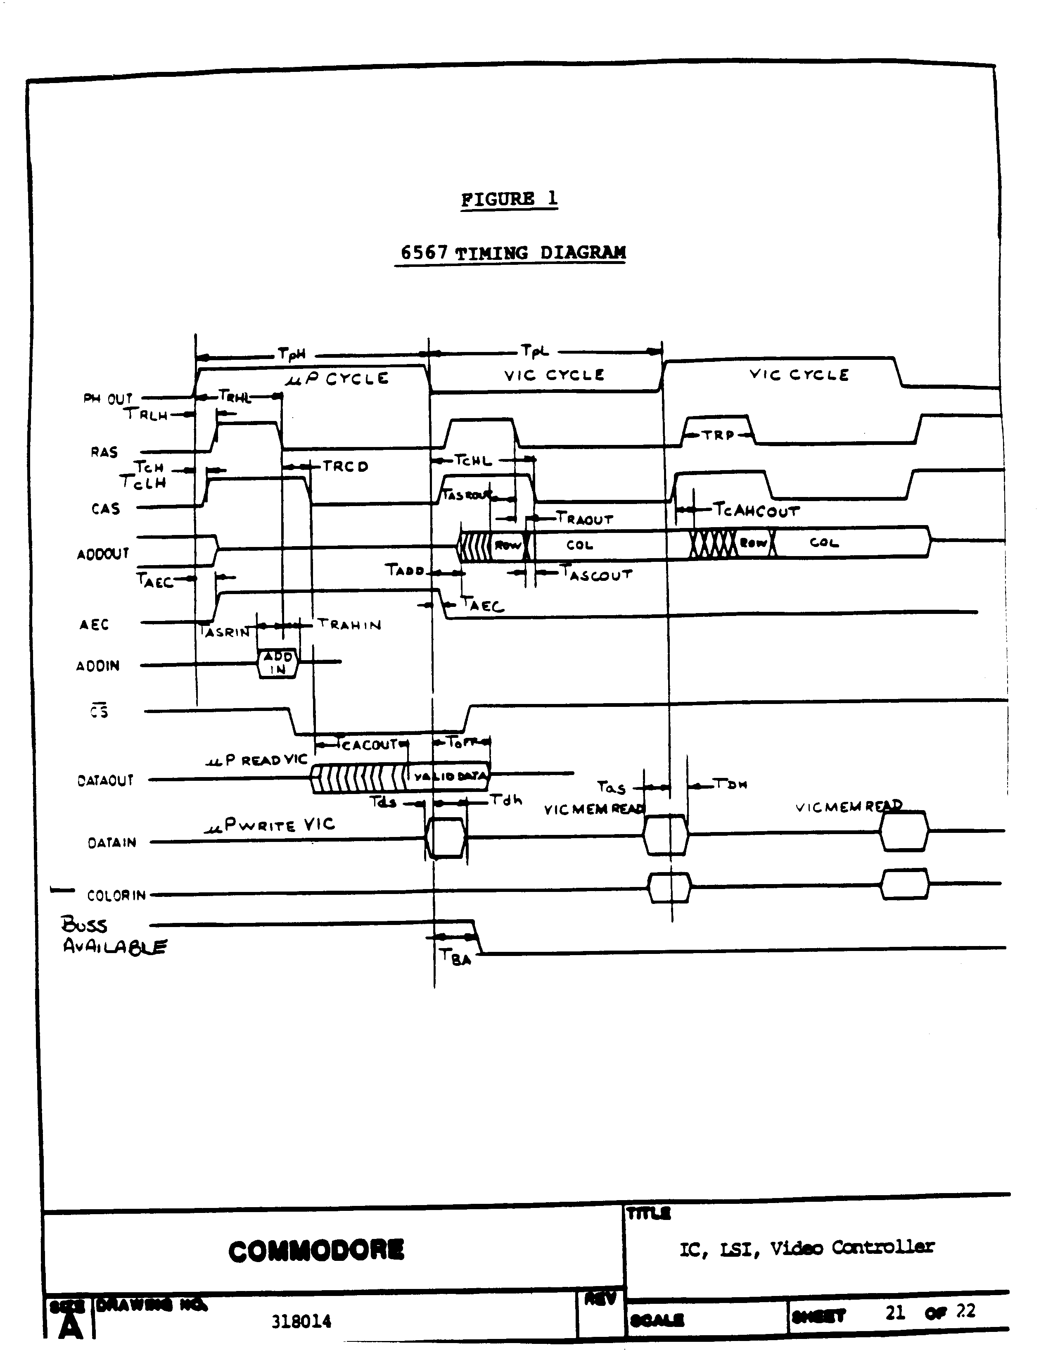
VIC/6567/6567-21.GIF
