svpetry/SP-C64/VIC/100110b_video.png

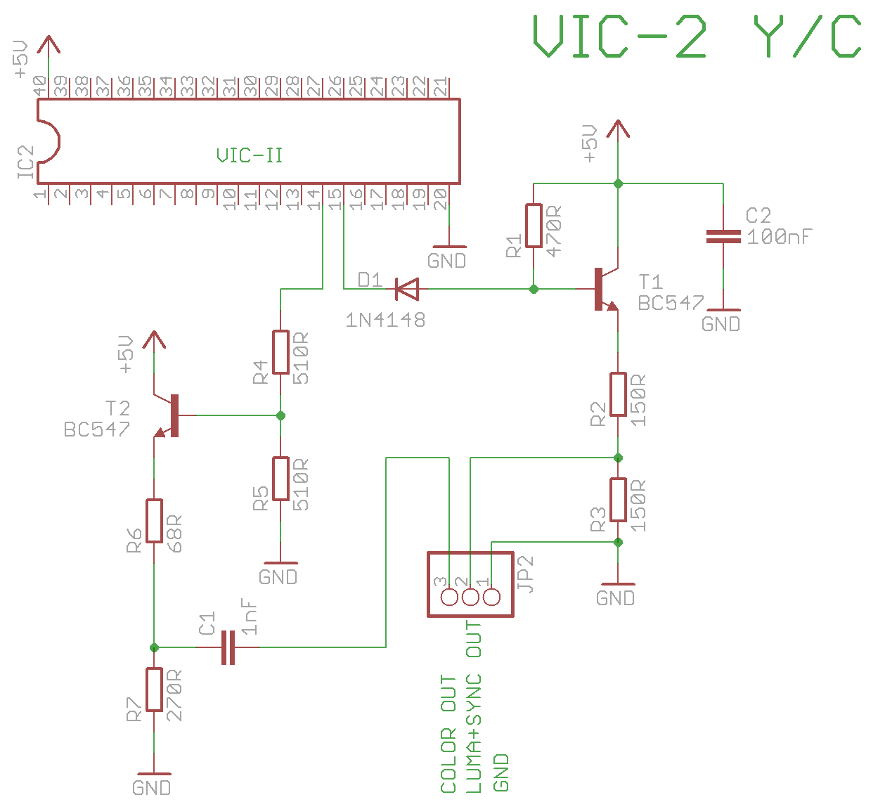
VIC/100110b_video.png
