svpetry/SP-C64/VIC/c64-scart-diagram.jpg

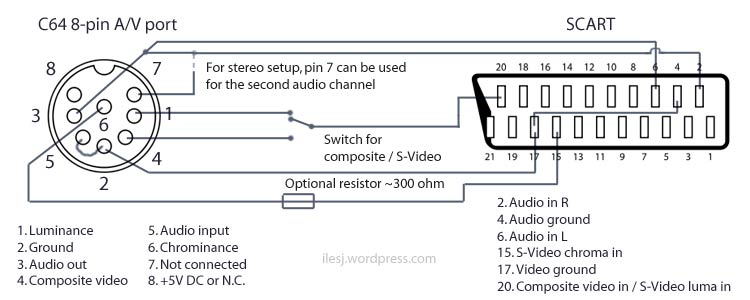
VIC/c64-scart-diagram.jpg
