svpetry/SP-C64/VIC/man-vic08.png

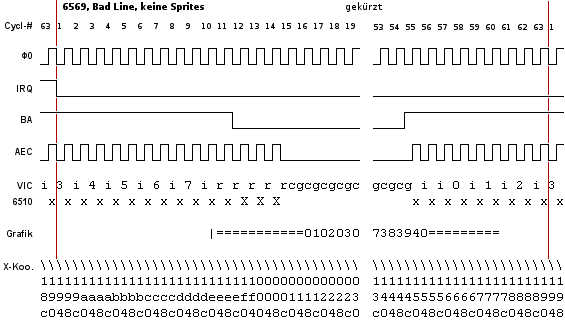
VIC/man-vic08.png
