svpetry/SP-C64/VIC/modulator-simple.png

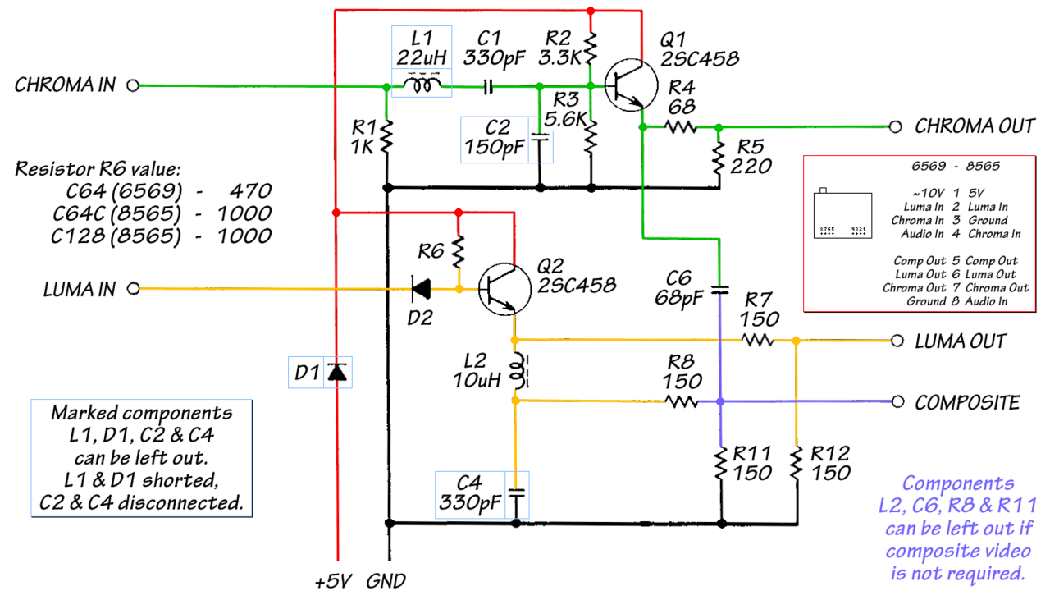
VIC/modulator-simple.png
