svpetry/SP-C64/VIC/WalkThatWay_V93_Schaltplan.png

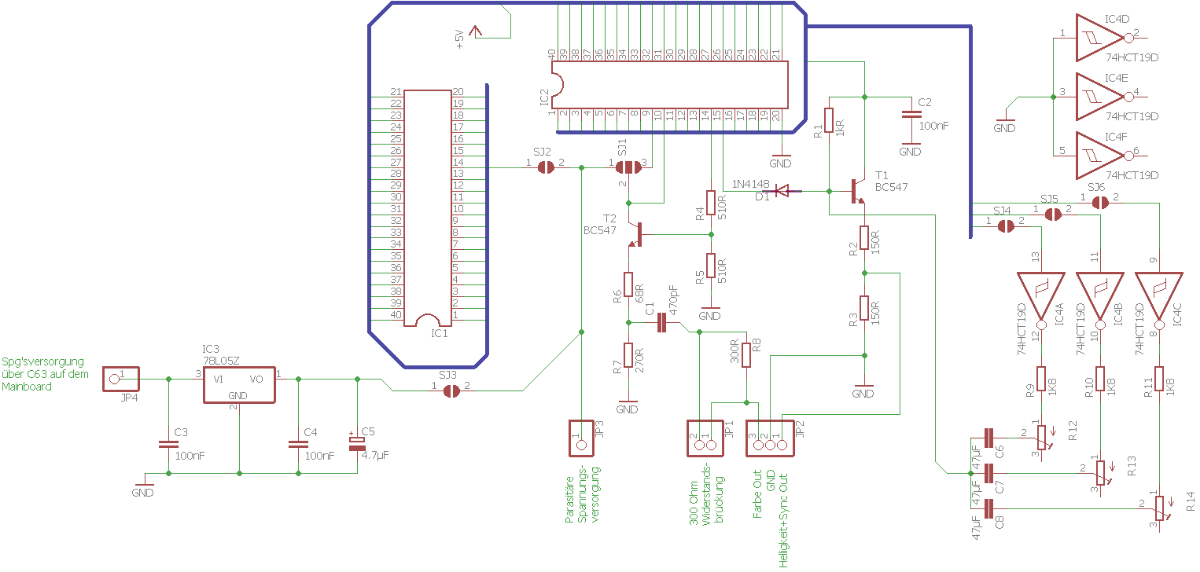
VIC/WalkThatWay_V93_Schaltplan.png
