svpetry/SP-C64/VIC/Zeichensatz-c64-poke1.jpg

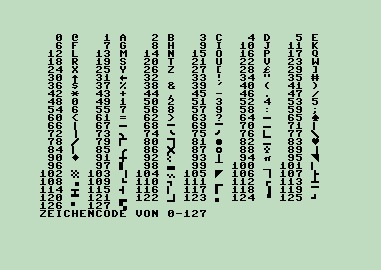
VIC/Zeichensatz-c64-poke1.jpg
