svpetry/SP-C64/VIC/Zeichensatz-c64-poke2.jpg

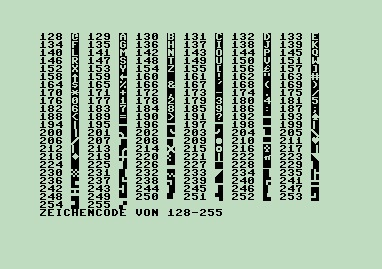
VIC/Zeichensatz-c64-poke2.jpg
