svpetry/SP-C64/Keyboard/C64BT_service_manual.png

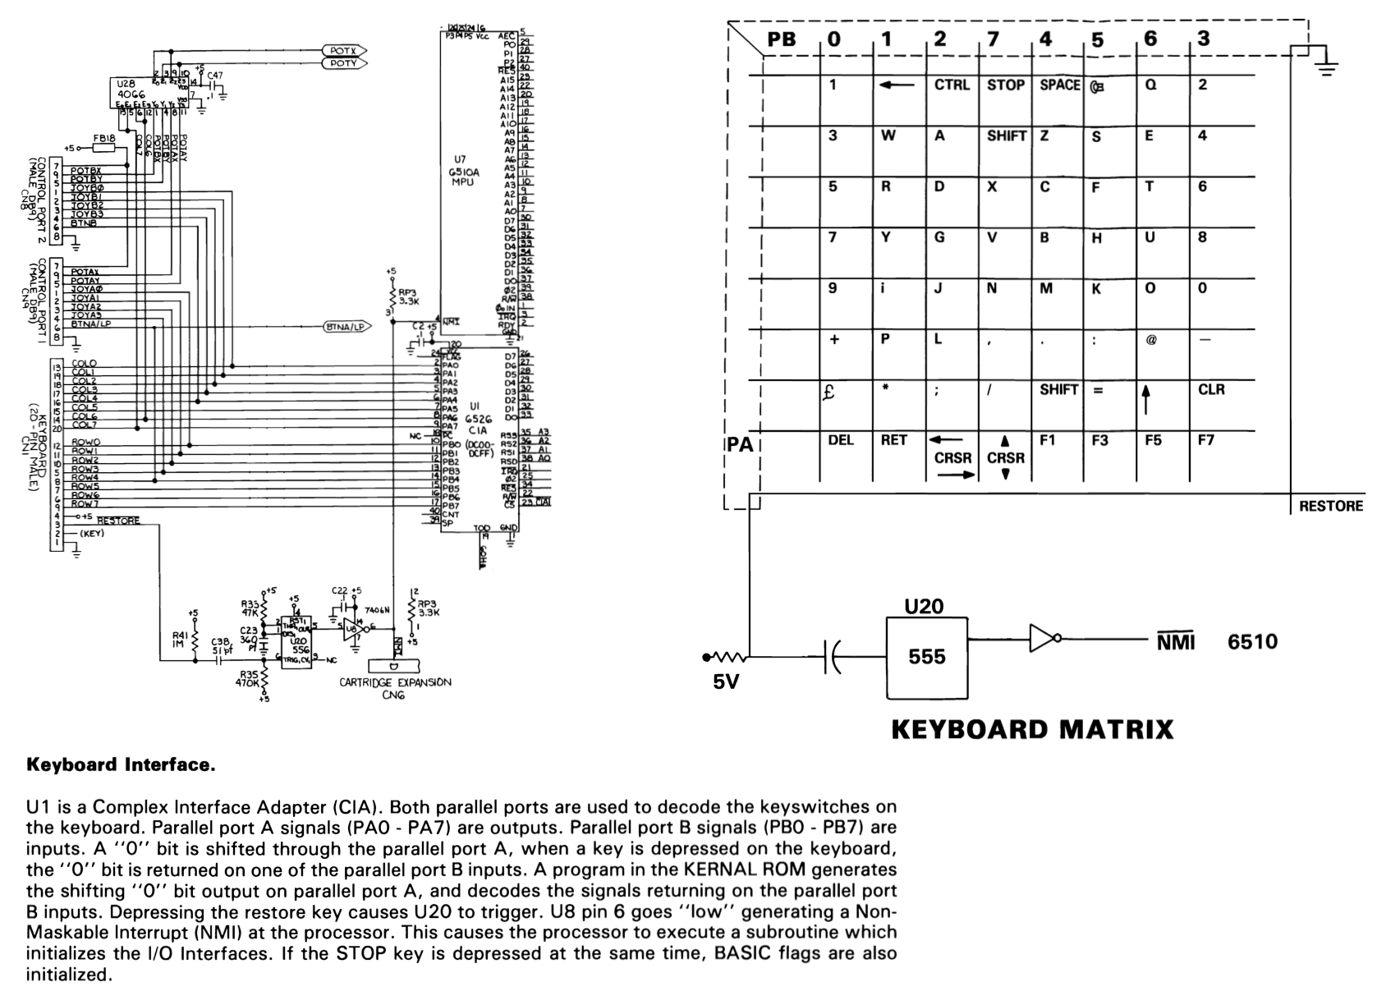
Keyboard/C64BT_service_manual.png
