svpetry/SP-C64/MPLAB/config.h

/* 
 * File:   config.h
 * Author: svpet
 *
 * Created on 4. März 2019, 19:30
 */

// CONFIG1H
#pragma config OSC = ECIO       // Oscillator Selection bits (EC oscillator, port function on RA6)
#pragma config FSCM = OFF       // Fail-Safe Clock Monitor Enable bit (Fail-Safe Clock Monitor disabled)
#pragma config IESO = OFF       // Internal External Switchover bit (Internal External Switchover mode disabled)

// CONFIG2L
#pragma config PWRT = OFF       // Power-up Timer Enable bit (PWRT enabled)
#pragma config BOR = OFF        // Brown-out Reset Enable bit (Brown-out Reset disabled)
// BORV = No Setting

// CONFIG2H
#pragma config WDT = OFF        // Watchdog Timer Enable bit (WDT disabled (control is placed on the SWDTEN bit))
#pragma config WDTPS = 32768    // Watchdog Timer Postscale Select bits (1:32768)

// CONFIG3H
#pragma config MCLRE = ON       // MCLR Pin Enable bit (MCLR pin enabled, RA5 input pin disabled)

// CONFIG4L
#pragma config STVR = OFF       // Stack Full/Underflow Reset Enable bit (Stack full/underflow will not cause Reset)
#pragma config LVP = OFF        // Low-Voltage ICSP Enable bit (Low-Voltage ICSP disabled)

// CONFIG5L
#pragma config CP0 = OFF        // Code Protection bit (Block 0 (00200-0007FFh) not code-protected)
#pragma config CP1 = OFF        // Code Protection bit (Block 1 (000800-000FFFh) not code-protected)

// CONFIG5H
#pragma config CPB = OFF        // Boot Block Code Protection bit (Boot Block (000000-0001FFh) not code-protected)
#pragma config CPD = OFF        // Data EEPROM Code Protection bit (Data EEPROM not code-protected)

// CONFIG6L
#pragma config WRT0 = OFF       // Write Protection bit (Block 0 (00200-0007FFh) not write-protected)
#pragma config WRT1 = OFF       // Write Protection bit (Block 1 (000800-000FFFh) not write-protected)

// CONFIG6H
#pragma config WRTC = OFF       // Configuration Register Write Protection bit (Configuration registers (300000-3000FFh) not write-protected)
#pragma config WRTB = OFF       // Boot Block Write Protection bit (Boot Block (000000-0001FFh) not write-protected)
#pragma config WRTD = OFF       // Data EEPROM Write Protection bit (Data EEPROM not write-protected)

// CONFIG7L
#pragma config EBTR0 = OFF      // Table Read Protection bit (Block 0 (00200-0007FFh) not protected from table reads executed in other blocks)
#pragma config EBTR1 = OFF      // Table Read Protection bit (Block 1 (000800-000FFFh) not protected from table reads executed in other blocks)

// CONFIG7H
#pragma config EBTRB = OFF      // Boot Block Table Read Protection bit (Boot Block (000000-0001FFh) not protected from table reads executed in other blocks)

// #pragma config statements should precede project file includes.
// Use project enums instead of #define for ON and OFF.

// -----------------------------------------------------------------------------

#define RS LATBbits.LB2
#define EN LATBbits.LB3
#define D4 LATBbits.LB4
#define D5 LATBbits.LB5
#define D6 LATBbits.LB6
#define D7 LATBbits.LB7
